Myuu1967/TB-04/ver2/hardware/基板分割_0824/TB04_1_alu/TB04_1_alu.kicad_sch

## KiCad design ver2/hardware/基板分割_0824/TB04_1_alu/TB04_1_alu.kicad_sch (2026-08-24)

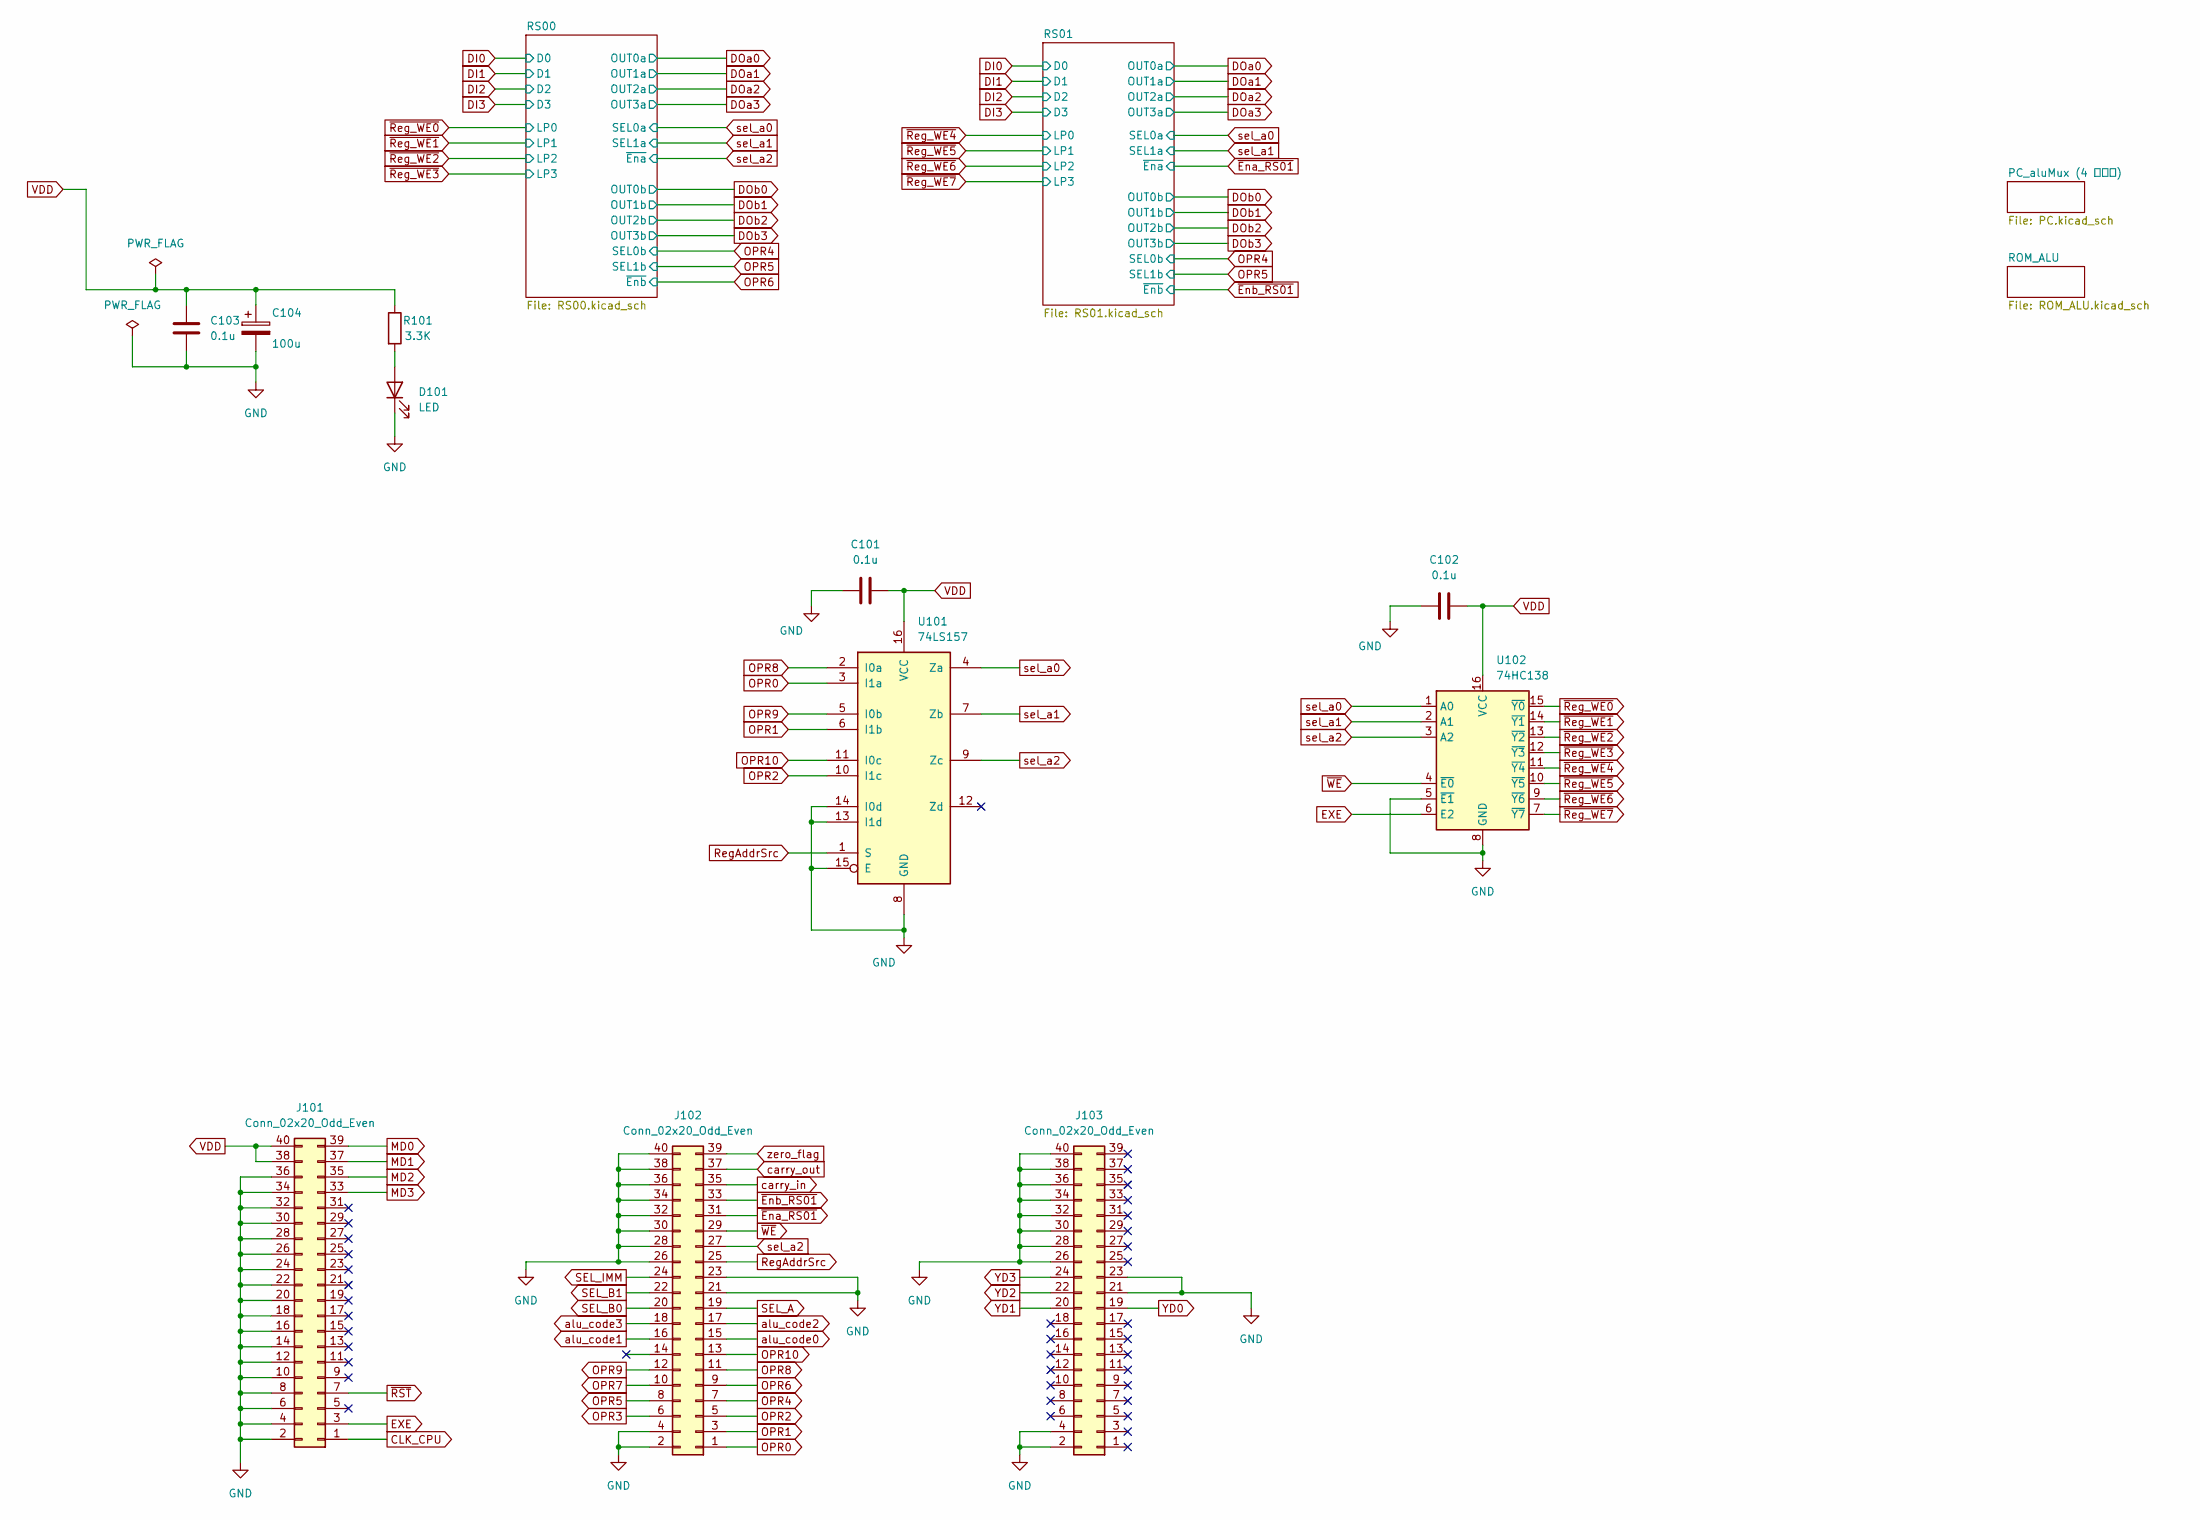
[picture p38: schematic TB04_1_alu.kicad_sch]

Parts:
C101, C102, C103: 0.1u; C_Disc_D4.3mm_W1.9mm_P5.00mm
C104: 100u; CP_Radial_D5.0mm_P2.00mm
D101: LED; LED_D3.0mm_Clear
J101, J102, J103: Conn_02x20_Odd_Even
R101: 3.3K; R_Axial_DIN0207_L6.3mm_D2.5mm_P7.62mm_Horizontal
U101: 74LS157
U102: 74HC138; DIP-16_W7.62mm_Socket

Connections:
CLK_CPU: J101.1
EXE: J101.3, U102.6 (E2)
GND: C101.2, C102.2, C103.2, C104.2, D101.1 (K), J101.2, J101.4, J101.6, J101.8, J101.10, J101.12, J101.14, J101.16, J101.18, J101.20, J101.22, J101.24, J101.26, J101.28, J101.30, J101.32, J101.34, J101.36, J102.2, J102.4, J102.21, J102.23, J102.26, J102.28, J102.30, J102.32, J102.34, J102.36, J102.38, J102.40, J103.2, J103.4, J103.21, J103.23, J103.26, J103.28, J103.30, J103.32, J103.34, J103.36, J103.38, J103.40, U101.8 (GND), U101.13 (I1d), U101.14 (I0d), U101.15 (E), U102.5 (~E1), U102.8 (GND)
MD0: J101.39
MD1: J101.37
MD2: J101.35
MD3: J101.33
unnamed: D101.2 (A), R101.2
OPR0: J102.1, U101.3 (I1a)
OPR1: J102.3, U101.6 (I1b)
OPR2: J102.5, U101.10 (I1c)
OPR3: J102.6
OPR4: J102.7
OPR5: J102.8
OPR6: J102.9
OPR7: J102.10
OPR8: J102.11, U101.2 (I0a)
OPR9: J102.12, U101.5 (I0b)
OPR10: J102.13, U101.11 (I0c)
RegAddrSrc: J102.25, U101.1 (S)
SEL_A: J102.19
SEL_B0: J102.20
SEL_B1: J102.22
SEL_IMM: J102.24
VDD: C101.1, C102.1, C103.1, C104.1, J101.38, J101.40, R101.1, U101.16 (VCC), U102.16 (VCC)
YD0: J103.19
YD1: J103.20
YD2: J103.22
YD3: J103.24
alu_code0: J102.15
alu_code1: J102.16
alu_code2: J102.17
alu_code3: J102.18
carry_in: J102.35
carry_out: J102.37
sel_a0: U101.4 (Za), U102.1 (A0)
sel_a1: U101.7 (Zb), U102.2 (A1)
sel_a2: J102.27, U101.9 (Zc), U102.3 (A2)
zero_flag: J102.39
~Ena_RS01: J102.31
~Enb_RS01: J102.33
~RST: J101.7
~Reg_WE0: U102.15 (~Y0)
~Reg_WE1: U102.14 (~Y1)
~Reg_WE2: U102.13 (~Y2)
~Reg_WE3: U102.12 (~Y3)
~Reg_WE4: U102.11 (~Y4)
~Reg_WE5: U102.10 (~Y5)
~Reg_WE6: U102.9 (~Y6)
~Reg_WE7: U102.7 (~Y7)
~WE: J102.29, U102.4 (~E0)
