Myuu1967/TB-04/ver2/hardware/基板分割_0824/TB04_2_ctrl/ALU.kicad_sch

## KiCad design ver2/hardware/基板分割_0824/TB04_2_ctrl/ALU.kicad_sch (2026-08-24)

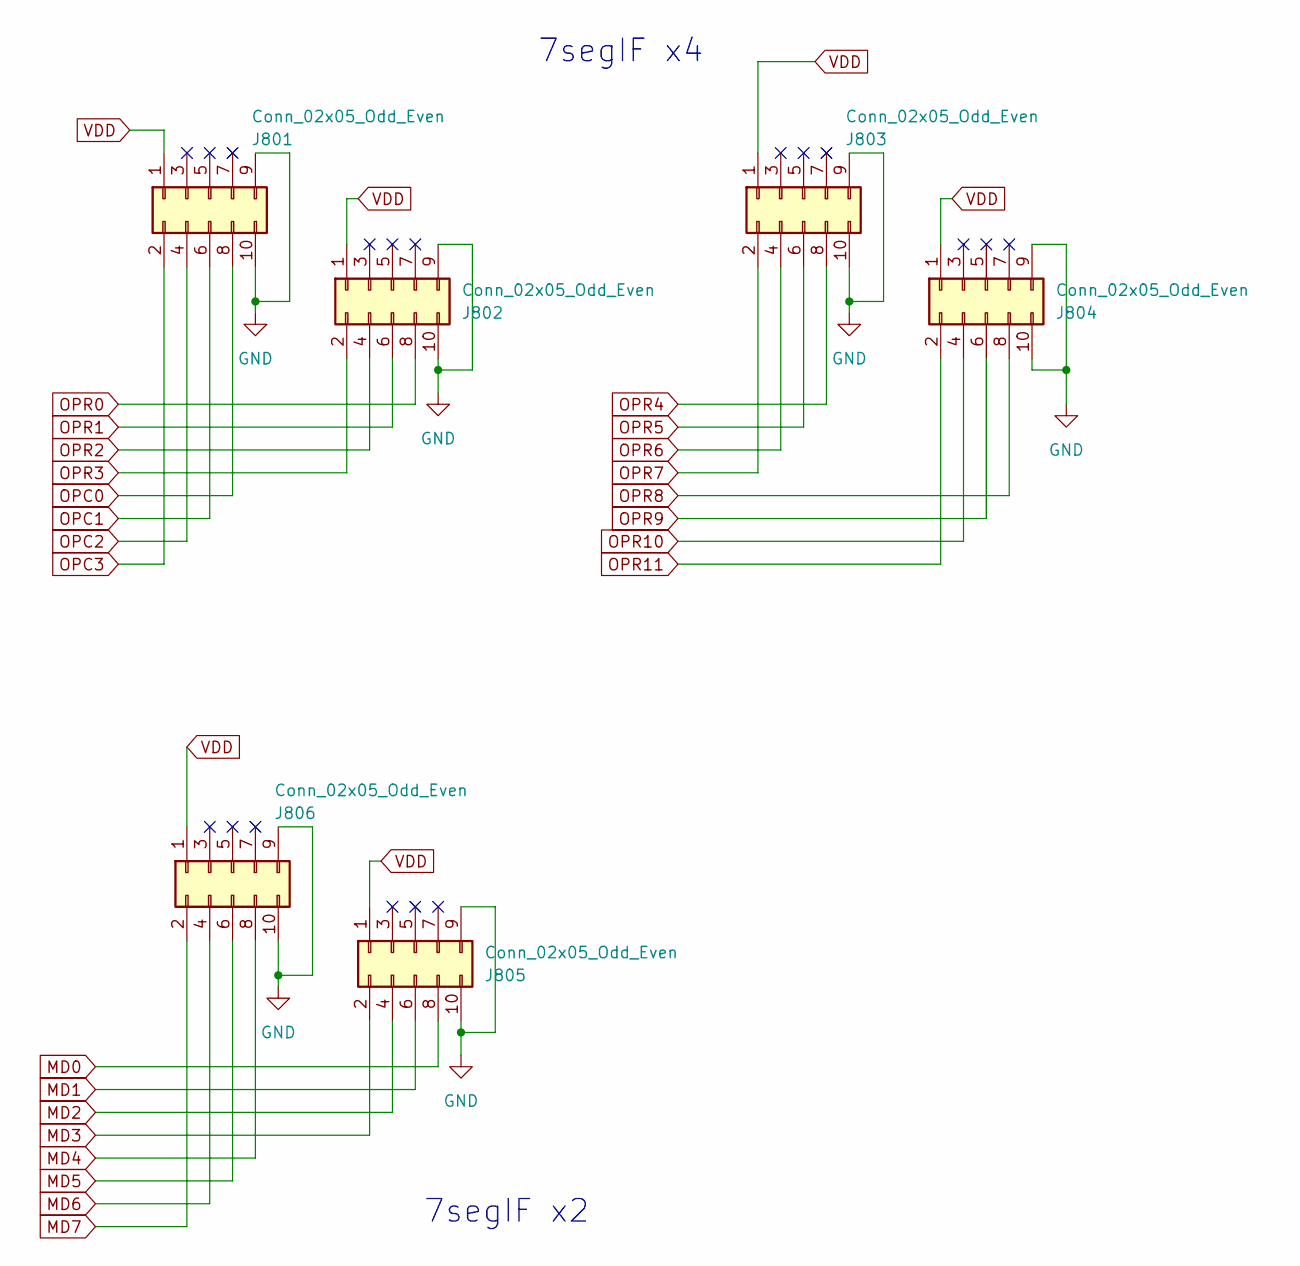
[picture p39: schematic ALU.kicad_sch]

Parts:
J801, J802, J803, J804, J805, J806: Conn_02x05_Odd_Even

Connections:
GND: J801.9, J801.10, J802.9, J802.10, J803.9, J803.10, J804.9, J804.10, J805.9, J805.10, J806.9, J806.10
MD0: J805.8
MD1: J805.6
MD2: J805.4
MD3: J805.2
MD4: J806.8
MD5: J806.6
MD6: J806.4
MD7: J806.2
OPC0: J801.8
OPC1: J801.6
OPC2: J801.4
OPC3: J801.2
OPR0: J802.8
OPR1: J802.6
OPR2: J802.4
OPR3: J802.2
OPR4: J803.8
OPR5: J803.6
OPR6: J803.4
OPR7: J803.2
OPR8: J804.8
OPR9: J804.6
OPR10: J804.4
OPR11: J804.2
VDD: J801.1, J802.1, J803.1, J804.1, J805.1, J806.1

Notes on the sheet:
7segIF x4
7segIF x2
