Myuu1967/TB-04/ver2/hardware/基板分割_0824/TB04_2_ctrl/AddrDecord.kicad_sch

## KiCad design ver2/hardware/基板分割_0824/TB04_2_ctrl/AddrDecord.kicad_sch (2026-08-24)

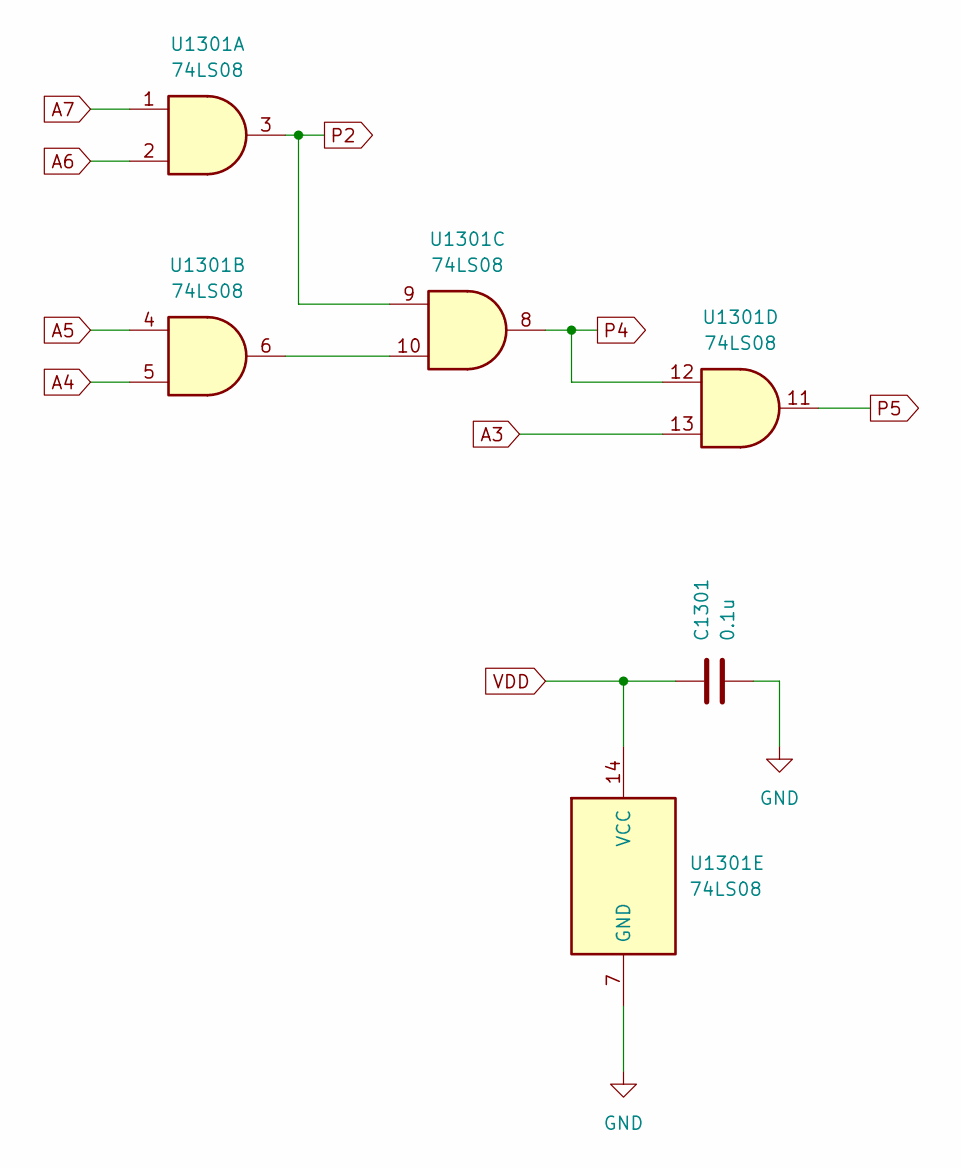
[picture p40: schematic AddrDecord.kicad_sch]

Parts:
C1301: 0.1u
U1301: 74LS08

Connections:
A3: U1301.13
A4: U1301.5
A5: U1301.4
A6: U1301.2
A7: U1301.1
GND: C1301.2, U1301.7 (GND)
unnamed: U1301.6, U1301.10
P2: U1301.3, U1301.9
P4: U1301.8, U1301.12
P5: U1301.11
VDD: C1301.1, U1301.14 (VCC)
