Myuu1967/TB-04/ver2/hardware/基板分割_0824/TB04_2_ctrl/Decoder.kicad_sch

## KiCad design ver2/hardware/基板分割_0824/TB04_2_ctrl/Decoder.kicad_sch (2026-08-24)

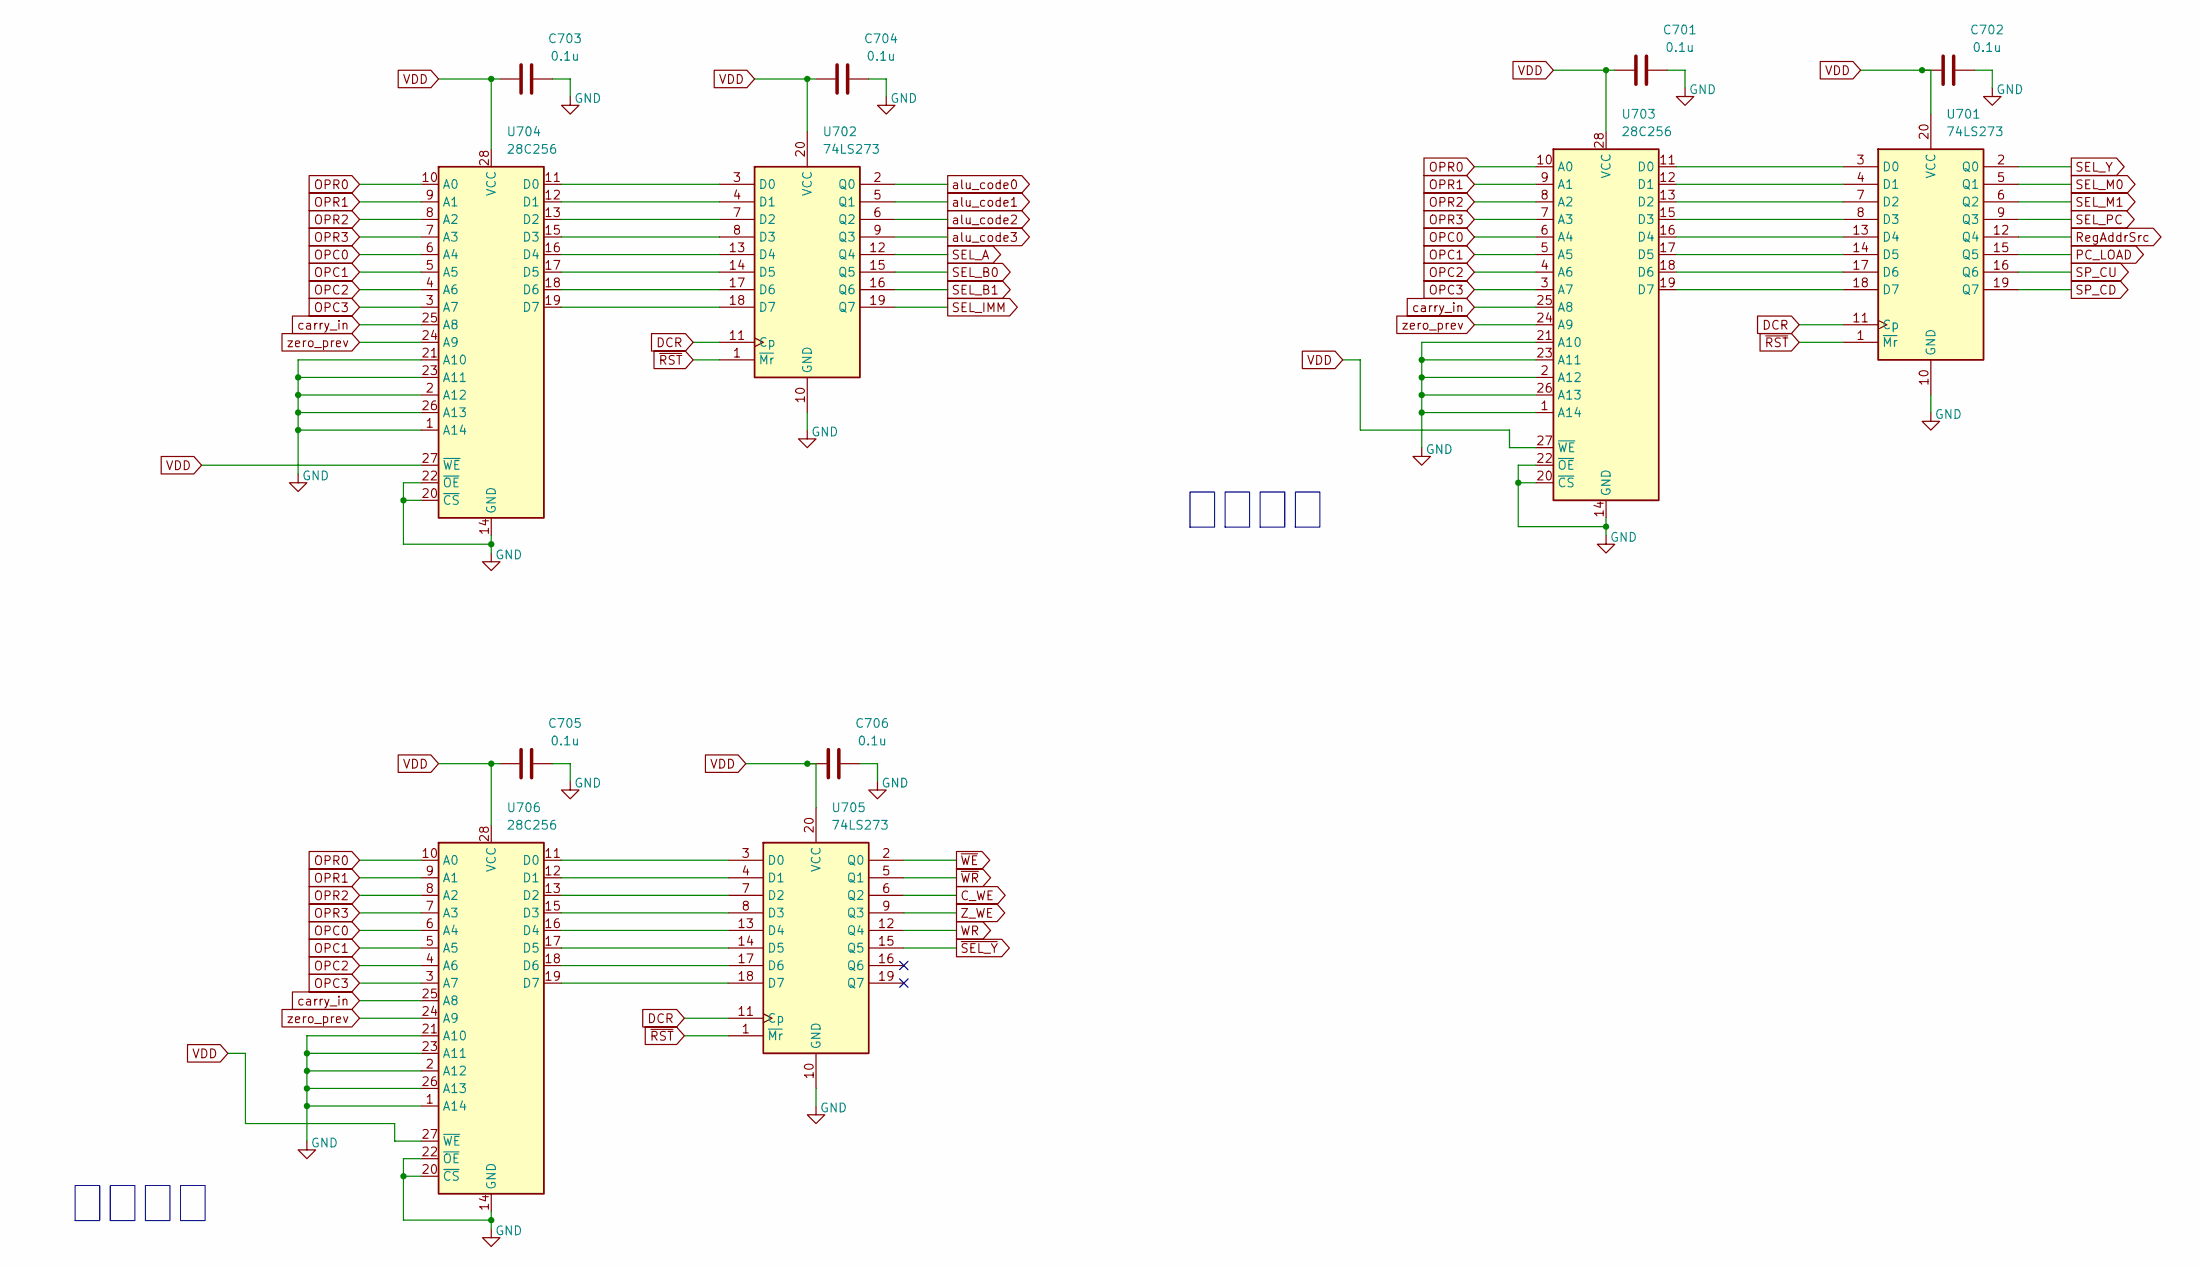
[picture p41: schematic Decoder.kicad_sch]

Parts:
C701, C702, C703, C704, C705, C706: 0.1u; C_Disc_D4.3mm_W1.9mm_P5.00mm
U701, U702, U705: 74LS273; DIP-20_W7.62mm_Socket
U703, U704, U706: 28C256; DIP-28_W15.24mm_Socket

Connections:
C_WE: U705.6 (Q2)
DCR: U701.11 (Cp), U702.11 (Cp), U705.11 (Cp)
GND: C701.1, C702.1, C703.1, C704.1, C705.1, C706.1, U701.10 (GND), U702.10 (GND), U703.1 (A14), U703.2 (A12), U703.14 (GND), U703.20 (~CS), U703.21 (A10), U703.22 (~OE), U703.23 (A11), U703.26 (A13), U704.1 (A14), U704.2 (A12), U704.14 (GND), U704.20 (~CS), U704.21 (A10), U704.22 (~OE), U704.23 (A11), U704.26 (A13), U705.10 (GND), U706.1 (A14), U706.2 (A12), U706.14 (GND), U706.20 (~CS), U706.21 (A10), U706.22 (~OE), U706.23 (A11), U706.26 (A13)
unnamed: U701.3 (D0), U703.11 (D0)
unnamed: U701.4 (D1), U703.12 (D1)
unnamed: U701.7 (D2), U703.13 (D2)
unnamed: U701.8 (D3), U703.15 (D3)
unnamed: U701.13 (D4), U703.16 (D4)
unnamed: U701.14 (D5), U703.17 (D5)
unnamed: U701.17 (D6), U703.18 (D6)
unnamed: U701.18 (D7), U703.19 (D7)
unnamed: U702.3 (D0), U704.11 (D0)
unnamed: U702.4 (D1), U704.12 (D1)
unnamed: U702.7 (D2), U704.13 (D2)
unnamed: U702.8 (D3), U704.15 (D3)
unnamed: U702.13 (D4), U704.16 (D4)
unnamed: U702.14 (D5), U704.17 (D5)
unnamed: U702.17 (D6), U704.18 (D6)
unnamed: U702.18 (D7), U704.19 (D7)
unnamed: U705.3 (D0), U706.11 (D0)
unnamed: U705.4 (D1), U706.12 (D1)
unnamed: U705.7 (D2), U706.13 (D2)
unnamed: U705.8 (D3), U706.15 (D3)
unnamed: U705.13 (D4), U706.16 (D4)
unnamed: U705.14 (D5), U706.17 (D5)
unnamed: U705.17 (D6), U706.18 (D6)
unnamed: U705.18 (D7), U706.19 (D7)
OPC0: U703.6 (A4), U704.6 (A4), U706.6 (A4)
OPC1: U703.5 (A5), U704.5 (A5), U706.5 (A5)
OPC2: U703.4 (A6), U704.4 (A6), U706.4 (A6)
OPC3: U703.3 (A7), U704.3 (A7), U706.3 (A7)
OPR0: U703.10 (A0), U704.10 (A0), U706.10 (A0)
OPR1: U703.9 (A1), U704.9 (A1), U706.9 (A1)
OPR2: U703.8 (A2), U704.8 (A2), U706.8 (A2)
OPR3: U703.7 (A3), U704.7 (A3), U706.7 (A3)
PC_LOAD: U701.15 (Q5)
RegAddrSrc: U701.12 (Q4)
SEL_A: U702.12 (Q4)
SEL_B0: U702.15 (Q5)
SEL_B1: U702.16 (Q6)
SEL_IMM: U702.19 (Q7)
SEL_M0: U701.5 (Q1)
SEL_M1: U701.6 (Q2)
SEL_PC: U701.9 (Q3)
SEL_Y: U701.2 (Q0)
SP_CD: U701.19 (Q7)
SP_CU: U701.16 (Q6)
VDD: C701.2, C702.2, C703.2, C704.2, C705.2, C706.2, U701.20 (VCC), U702.20 (VCC), U703.27 (~WE), U703.28 (VCC), U704.27 (~WE), U704.28 (VCC), U705.20 (VCC), U706.27 (~WE), U706.28 (VCC)
WR: U705.12 (Q4)
Z_WE: U705.9 (Q3)
alu_code0: U702.2 (Q0)
alu_code1: U702.5 (Q1)
alu_code2: U702.6 (Q2)
alu_code3: U702.9 (Q3)
carry_in: U703.25 (A8), U704.25 (A8), U706.25 (A8)
zero_prev: U703.24 (A9), U704.24 (A9), U706.24 (A9)
~RST: U701.1 (~Mr), U702.1 (~Mr), U705.1 (~Mr)
~SEL_Y: U705.15 (Q5)
~WE: U705.2 (Q0)
~WR: U705.5 (Q1)

Notes on the sheet:
デコーダ
