Myuu1967/TB-04/ver2/hardware/基板分割_0824/TB04_2_ctrl/TB04_2_ctrl.kicad_sch

## KiCad design ver2/hardware/基板分割_0824/TB04_2_ctrl/TB04_2_ctrl.kicad_sch (2026-08-24)

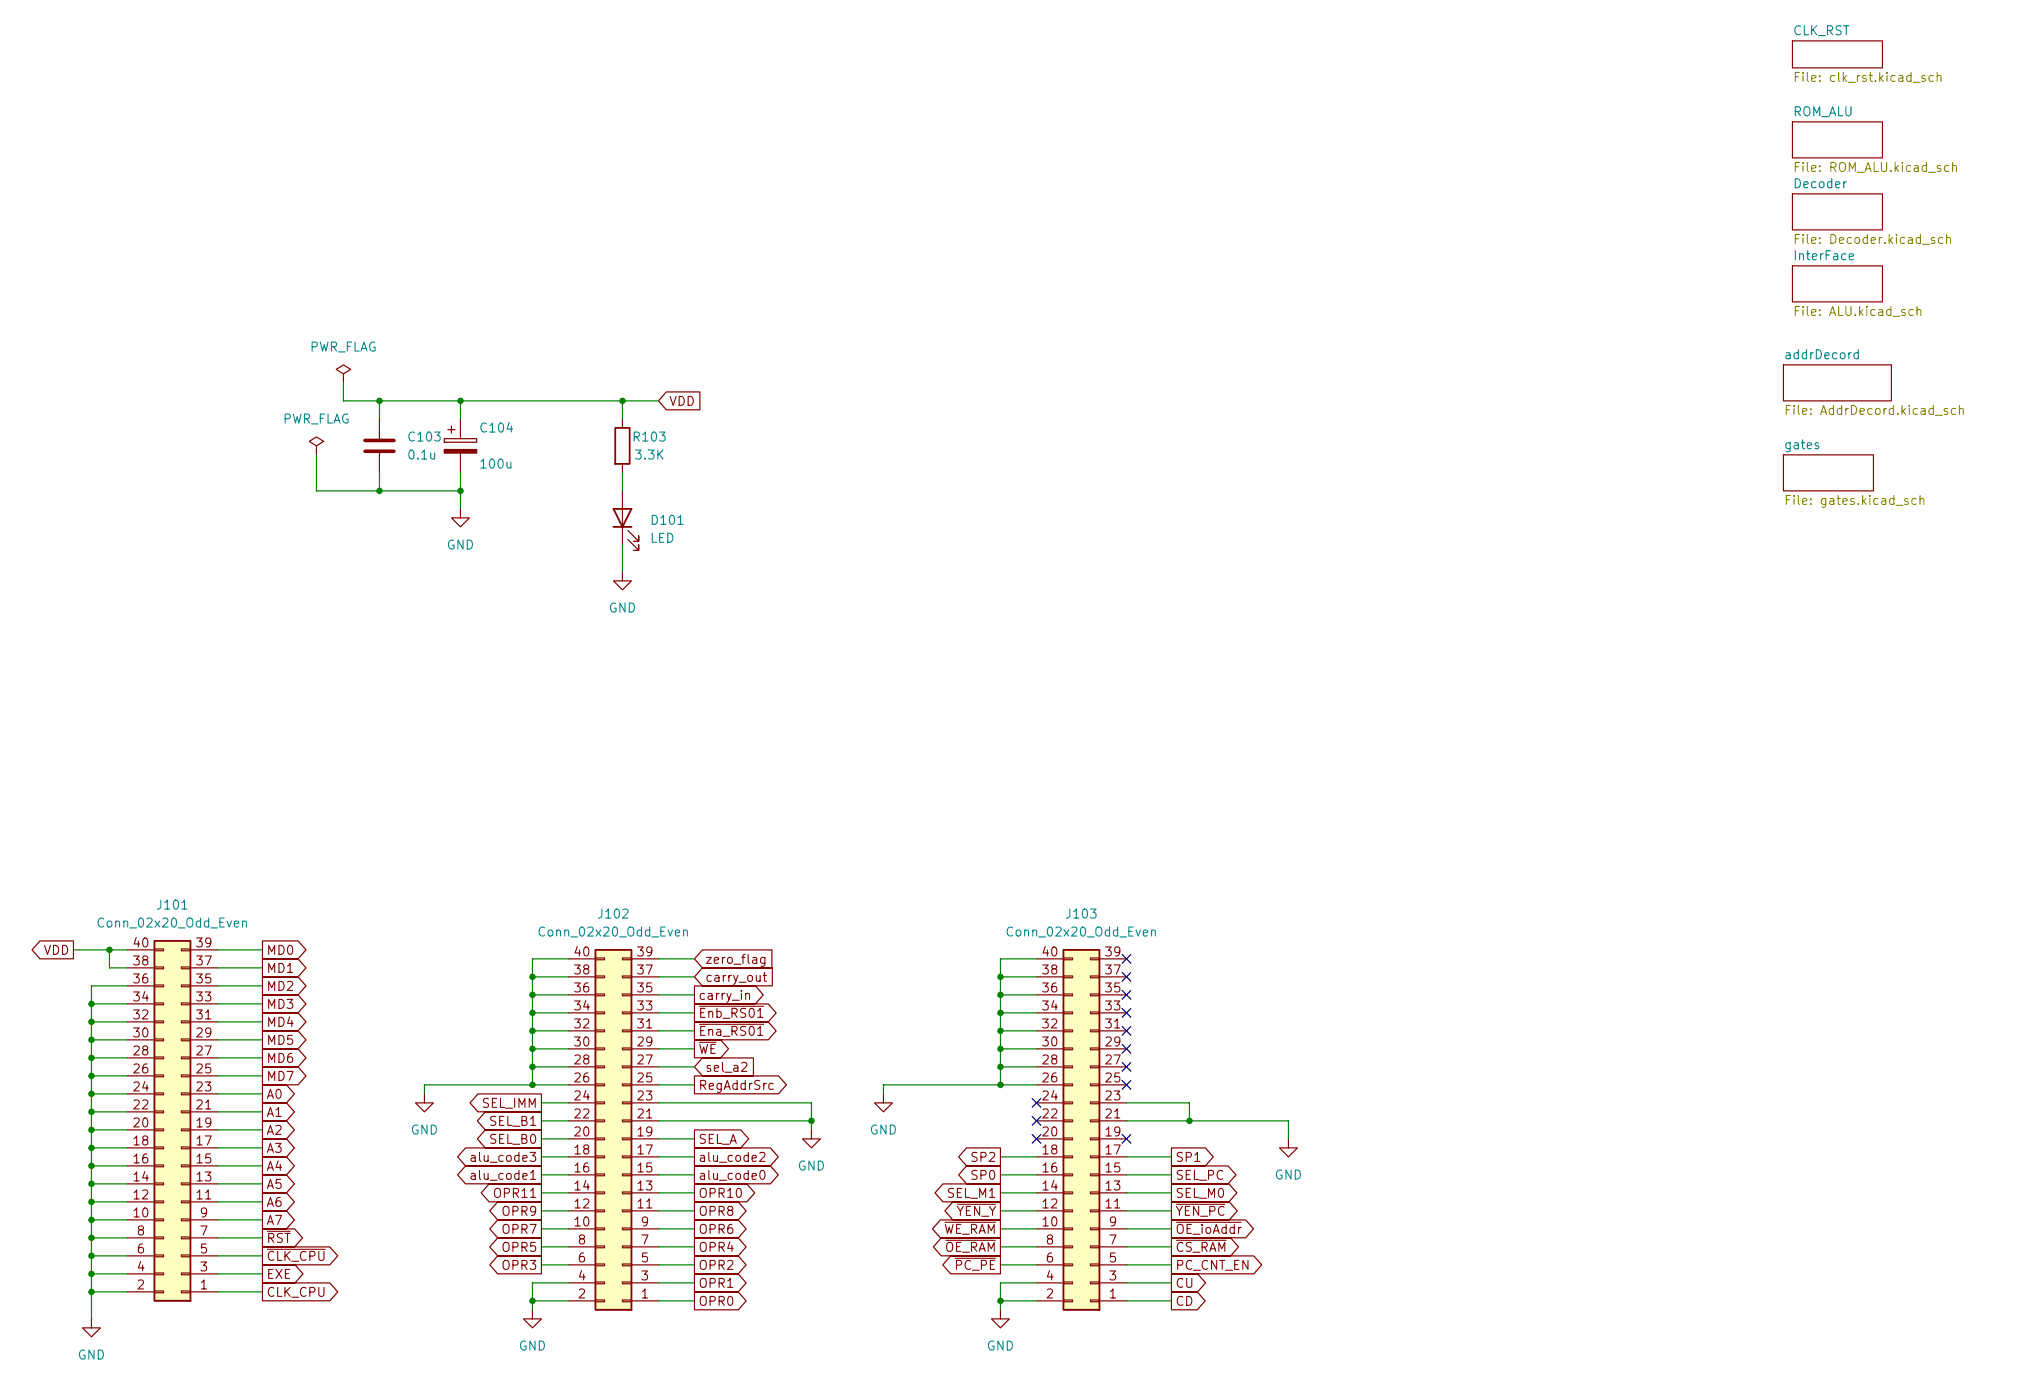
[picture p43: schematic TB04_2_ctrl.kicad_sch]

Parts:
C103: 0.1u; C_Disc_D4.3mm_W1.9mm_P5.00mm
C104: 100u; CP_Radial_D5.0mm_P2.00mm
D101: LED; LED_D3.0mm_Clear
J101, J102, J103: Conn_02x20_Odd_Even
R103: 3.3K; R_Axial_DIN0207_L6.3mm_D2.5mm_P7.62mm_Horizontal

Connections:
A0: J101.23
A1: J101.21
A2: J101.19
A3: J101.17
A4: J101.15
A5: J101.13
A6: J101.11
A7: J101.9
CD: J103.1
CLK_CPU: J101.1
CU: J103.3
EXE: J101.3
GND: C103.2, C104.2, D101.1 (K), J101.2, J101.4, J101.6, J101.8, J101.10, J101.12, J101.14, J101.16, J101.18, J101.20, J101.22, J101.24, J101.26, J101.28, J101.30, J101.32, J101.34, J101.36, J102.2, J102.4, J102.21, J102.23, J102.26, J102.28, J102.30, J102.32, J102.34, J102.36, J102.38, J102.40, J103.2, J103.4, J103.21, J103.23, J103.26, J103.28, J103.30, J103.32, J103.34, J103.36, J103.38, J103.40
MD0: J101.39
MD1: J101.37
MD2: J101.35
MD3: J101.33
MD4: J101.31
MD5: J101.29
MD6: J101.27
MD7: J101.25
unnamed: D101.2 (A), R103.2
OPR0: J102.1
OPR1: J102.3
OPR2: J102.5
OPR3: J102.6
OPR4: J102.7
OPR5: J102.8
OPR6: J102.9
OPR7: J102.10
OPR8: J102.11
OPR9: J102.12
OPR10: J102.13
OPR11: J102.14
PC_CNT_EN: J103.5
RegAddrSrc: J102.25
SEL_A: J102.19
SEL_B0: J102.20
SEL_B1: J102.22
SEL_IMM: J102.24
SEL_M0: J103.13
SEL_M1: J103.14
SEL_PC: J103.15
SP0: J103.16
SP1: J103.17
SP2: J103.18
VDD: C103.1, C104.1, J101.38, J101.40, R103.1
alu_code0: J102.15
alu_code1: J102.16
alu_code2: J102.17
alu_code3: J102.18
carry_in: J102.35
carry_out: J102.37
sel_a2: J102.27
zero_flag: J102.39
~CLK_CPU: J101.5
~CS_RAM: J103.7
~Ena_RS01: J102.31
~Enb_RS01: J102.33
~OE_RAM: J103.8
~OE_ioAddr: J103.9
~PC_PE: J103.6
~RST: J101.7
~WE_RAM: J103.10
~WE: J102.29
~YEN_PC: J103.11
~YEN_Y: J103.12
