Myuu1967/TB-04/ver2/hardware/基板分割_0824/TB04_2_ctrl/clk_rst.kicad_sch

## KiCad design ver2/hardware/基板分割_0824/TB04_2_ctrl/clk_rst.kicad_sch (2026-08-24)

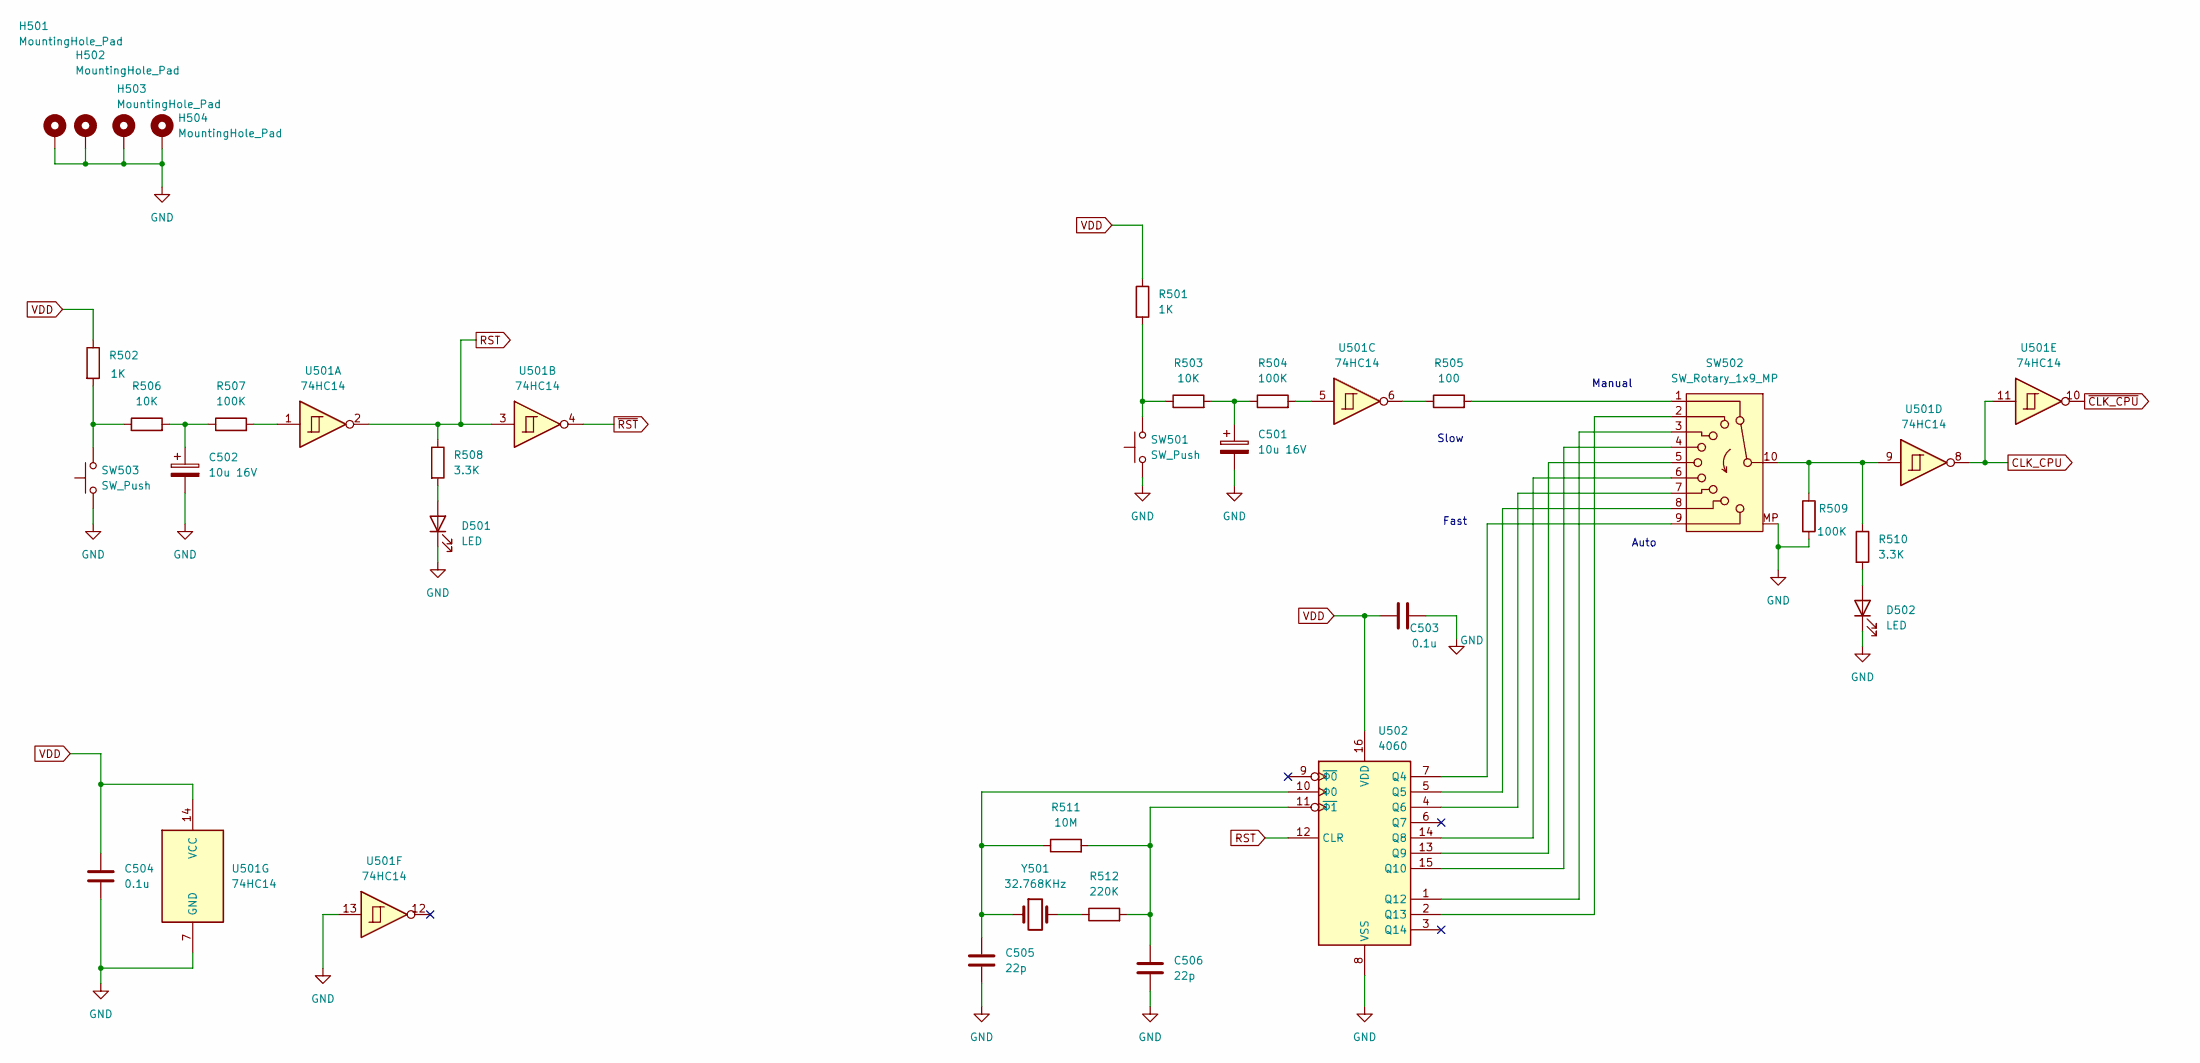
[picture p44: schematic clk_rst.kicad_sch]

Parts:
C501, C502: 10u 16V; CP_Radial_D5.0mm_P2.00mm
C503, C504: 0.1u; C_Disc_D4.3mm_W1.9mm_P5.00mm
C505, C506: 22p
D501, D502: LED; LED_D3.0mm_Clear
H501, H502, H503, H504: MountingHole_Pad; MountingHole_3.2mm_M3_Pad_Via
R501, R502: 1K; R_Axial_DIN0207_L6.3mm_D2.5mm_P10.16mm_Horizontal
R503, R506: 10K; R_Axial_DIN0207_L6.3mm_D2.5mm_P10.16mm_Horizontal
R504, R507: 100K; R_Axial_DIN0207_L6.3mm_D2.5mm_P7.62mm_Horizontal
R505: 100; R_Axial_DIN0207_L6.3mm_D2.5mm_P10.16mm_Horizontal
R508, R510: 3.3K; R_Axial_DIN0207_L6.3mm_D2.5mm_P7.62mm_Horizontal
R509: 100K
R511: 10M
R512: 220K
SW501, SW503: SW_Push; SW_Tactile_Straight_KSL0Axx1LFTR
SW502: SW_Rotary_1x9_MP
U501: 74HC14; DIP-14_W7.62mm_Socket
U502: 4060
Y501: 32.768KHz

Connections:
CLK_CPU: U501.8, U501.11
GND: C501.2, C502.2, C503.1, C504.2, C505.2, C506.2, D501.1 (K), D502.1 (K), H501.1, H502.1, H503.1, H504.1, R509.2, SW501.1, SW502.MP, SW503.1, U501.7 (GND), U501.13, U502.8 (VSS)
unnamed: C501.1, R503.2, R504.1
unnamed: C502.1, R506.2, R507.1
unnamed: C505.1, R511.1, U502.10 (Φ0), Y501.1
unnamed: C506.1, R511.2, R512.2, U502.11 (~Φ1)
unnamed: D501.2 (A), R508.2
unnamed: D502.2 (A), R510.2
unnamed: R501.2, R503.1, SW501.2
unnamed: R502.2, R506.1, SW503.2
unnamed: R504.2, U501.5
unnamed: R505.1, U501.6
unnamed: R505.2, SW502.1
unnamed: R507.2, U501.1
unnamed: R509.1, R510.1, SW502.10, U501.9
unnamed: R512.1, Y501.2
unnamed: SW502.2, U502.2 (Q13)
unnamed: SW502.3, U502.1 (Q12)
unnamed: SW502.4, U502.15 (Q10)
unnamed: SW502.5, U502.13 (Q9)
unnamed: SW502.6, U502.14 (Q8)
unnamed: SW502.7, U502.4 (Q6)
unnamed: SW502.8, U502.5 (Q5)
unnamed: SW502.9, U502.7 (Q4)
RST: R508.1, U501.2, U501.3, U502.12 (CLR)
VDD: C503.2, C504.1, R501.1, R502.1, U501.14 (VCC), U502.16 (VDD)
~CLK_CPU: U501.10
~RST: U501.4

Notes on the sheet:
Auto
Manual
Slow
Fast
