Myuu1967/TB-04/ver2/hardware/基板分割_0824/TB04_2_ctrl/gates.kicad_sch

## KiCad design ver2/hardware/基板分割_0824/TB04_2_ctrl/gates.kicad_sch (2026-08-24)

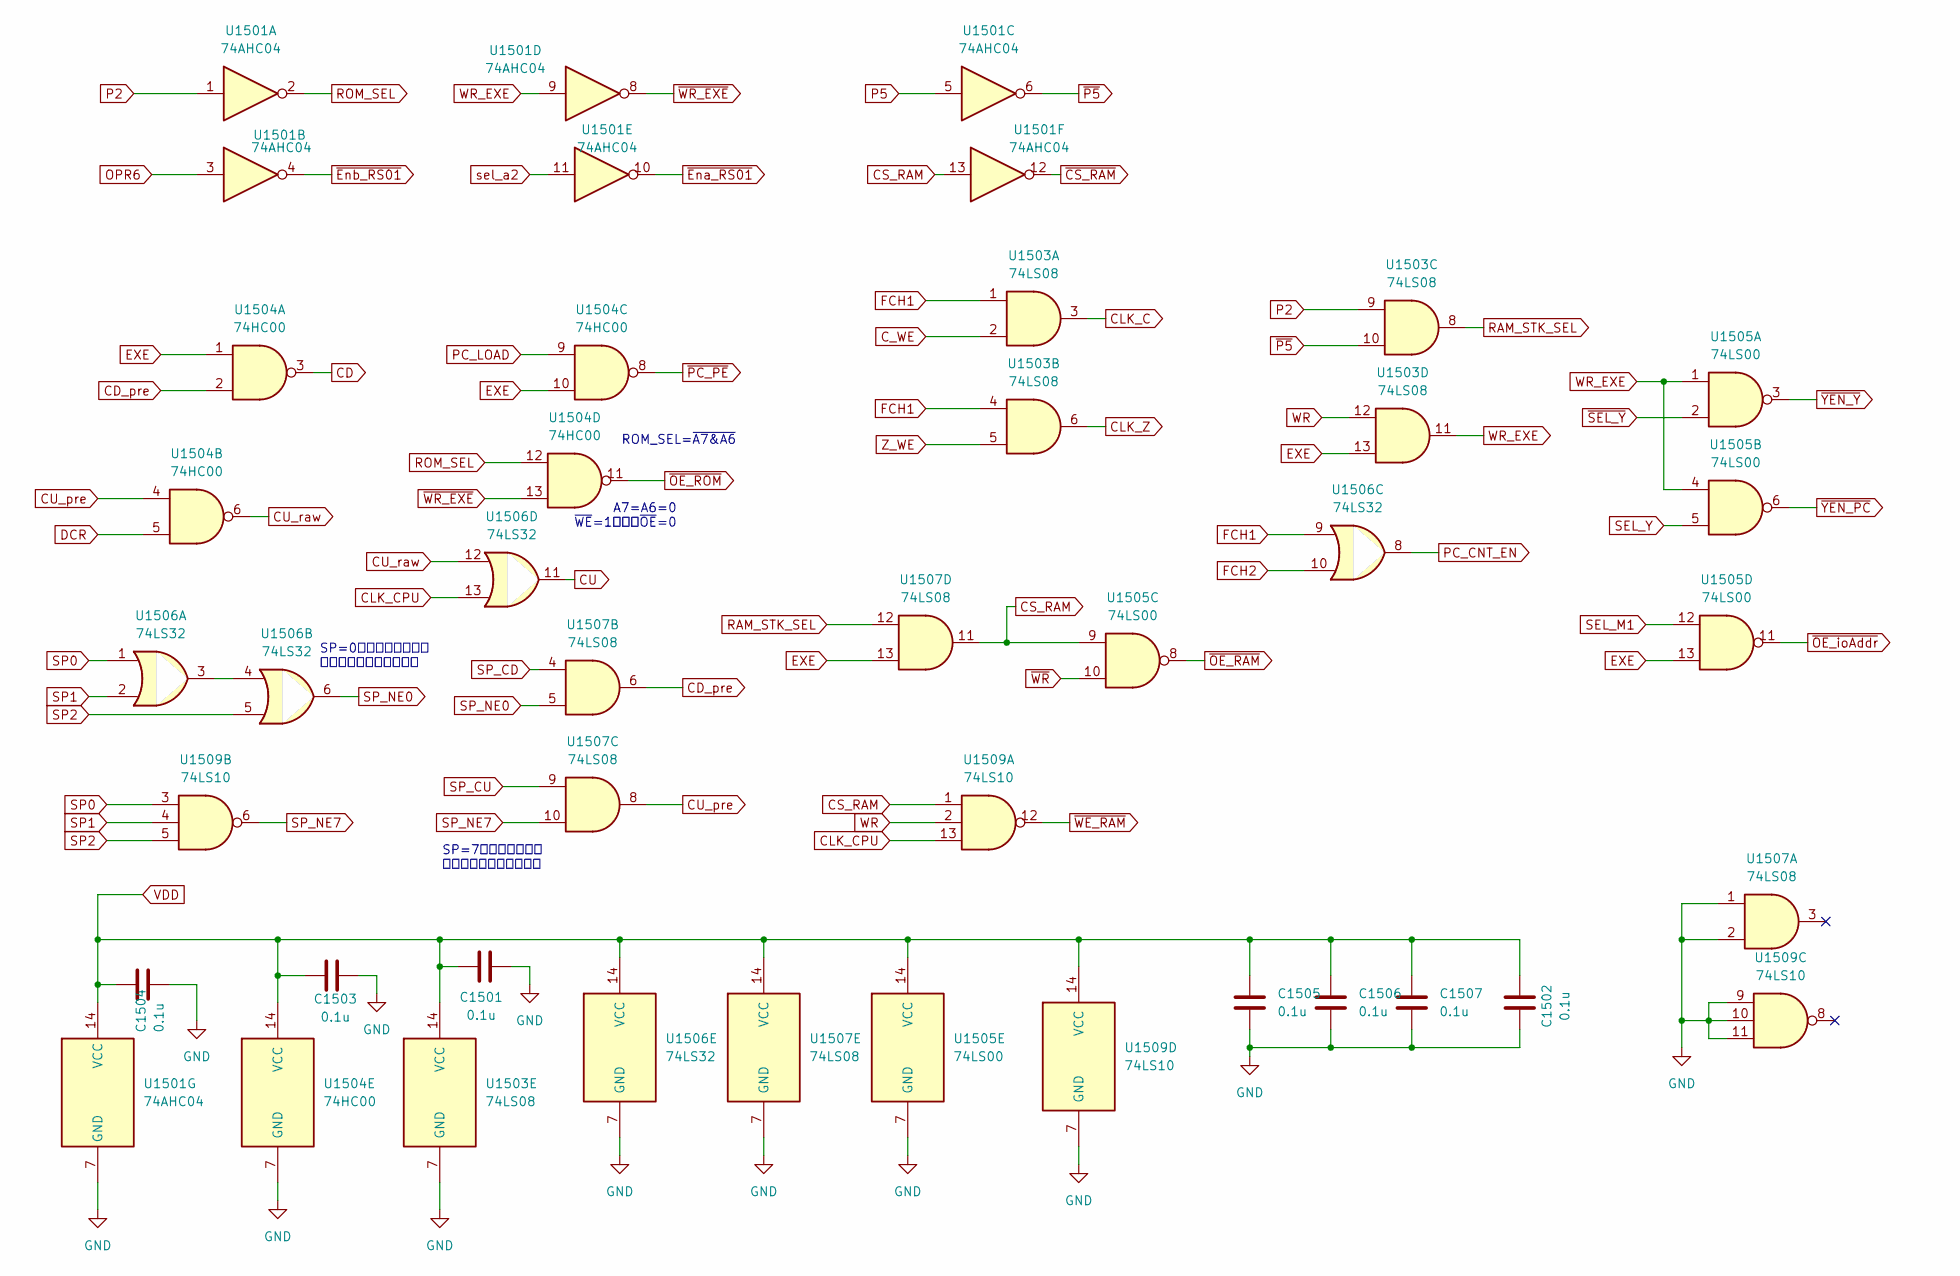
[picture p45: schematic gates.kicad_sch]

Parts:
C1501, C1502, C1503: 0.1u; C_Disc_D4.3mm_W1.9mm_P5.00mm
C1504, C1505, C1506, C1507: 0.1u
U1501: 74AHC04
U1503, U1507: 74LS08
U1504: 74HC00
U1505: 74LS00
U1506: 74LS32
U1509: 74LS10

Connections:
CD: U1504.3
CD_pre: U1504.2, U1507.6
CLK_C: U1503.3
CLK_CPU: U1506.13, U1509.13
CLK_Z: U1503.6
CS_RAM: U1501.13, U1505.9, U1507.11, U1509.1
CU: U1506.11
CU_pre: U1504.4, U1507.8
CU_raw: U1504.6, U1506.12
C_WE: U1503.2
DCR: U1504.5
EXE: U1503.13, U1504.1, U1504.10, U1505.13, U1507.13
FCH1: U1503.1, U1503.4, U1506.9
FCH2: U1506.10
GND: C1501.2, C1502.1, C1503.2, C1504.2, C1505.1, C1506.1, C1507.1, U1501.7 (GND), U1503.7 (GND), U1504.7 (GND), U1505.7 (GND), U1506.7 (GND), U1507.1, U1507.2, U1507.7 (GND), U1509.7 (GND), U1509.9, U1509.10, U1509.11
unnamed: U1506.3, U1506.4
OPR6: U1501.3
P2: U1501.1, U1503.9
P5: U1501.5
PC_CNT_EN: U1506.8
PC_LOAD: U1504.9
RAM_STK_SEL: U1503.8, U1507.12
ROM_SEL: U1501.2, U1504.12
SEL_M1: U1505.12
SEL_Y: U1505.5
SP0: U1506.1, U1509.3
SP1: U1506.2, U1509.4
SP2: U1506.5, U1509.5
SP_CD: U1507.4
SP_CU: U1507.9
SP_NE0: U1506.6, U1507.5
SP_NE7: U1507.10, U1509.6
VDD: C1501.1, C1502.2, C1503.1, C1504.1, C1505.2, C1506.2, C1507.2, U1501.14 (VCC), U1503.14 (VCC), U1504.14 (VCC), U1505.14 (VCC), U1506.14 (VCC), U1507.14 (VCC), U1509.14 (VCC)
WR: U1503.12, U1509.2
WR_EXE: U1501.9, U1503.11, U1505.1, U1505.4
Z_WE: U1503.5
sel_a2: U1501.11
~CS_RAM: U1501.12
~Ena_RS01: U1501.10
~Enb_RS01: U1501.4
~OE_RAM: U1505.8
~OE_ROM: U1504.11
~OE_ioAddr: U1505.11
~P5: U1501.6, U1503.10
~PC_PE: U1504.8
~SEL_Y: U1505.2
~WE_RAM: U1509.12
~WR_EXE: U1501.8, U1504.13
~WR: U1505.10
~YEN_PC: U1505.6
~YEN_Y: U1505.3

Notes on the sheet:
ROM_SEL=~{A7&A6}
A7=A6=0 ~{WE}=1のとき~{OE}=0
SP=7のときそれ以上 カウントアップさせない
SP=0のときそれ以下に カウントダウンさせない
