Myuu1967/TB-04/ver2/hardware/基板分割_0824/TB04_4_io/TB04_4_io.kicad_sch

## KiCad design ver2/hardware/基板分割_0824/TB04_4_io/TB04_4_io.kicad_sch (2026-08-24)

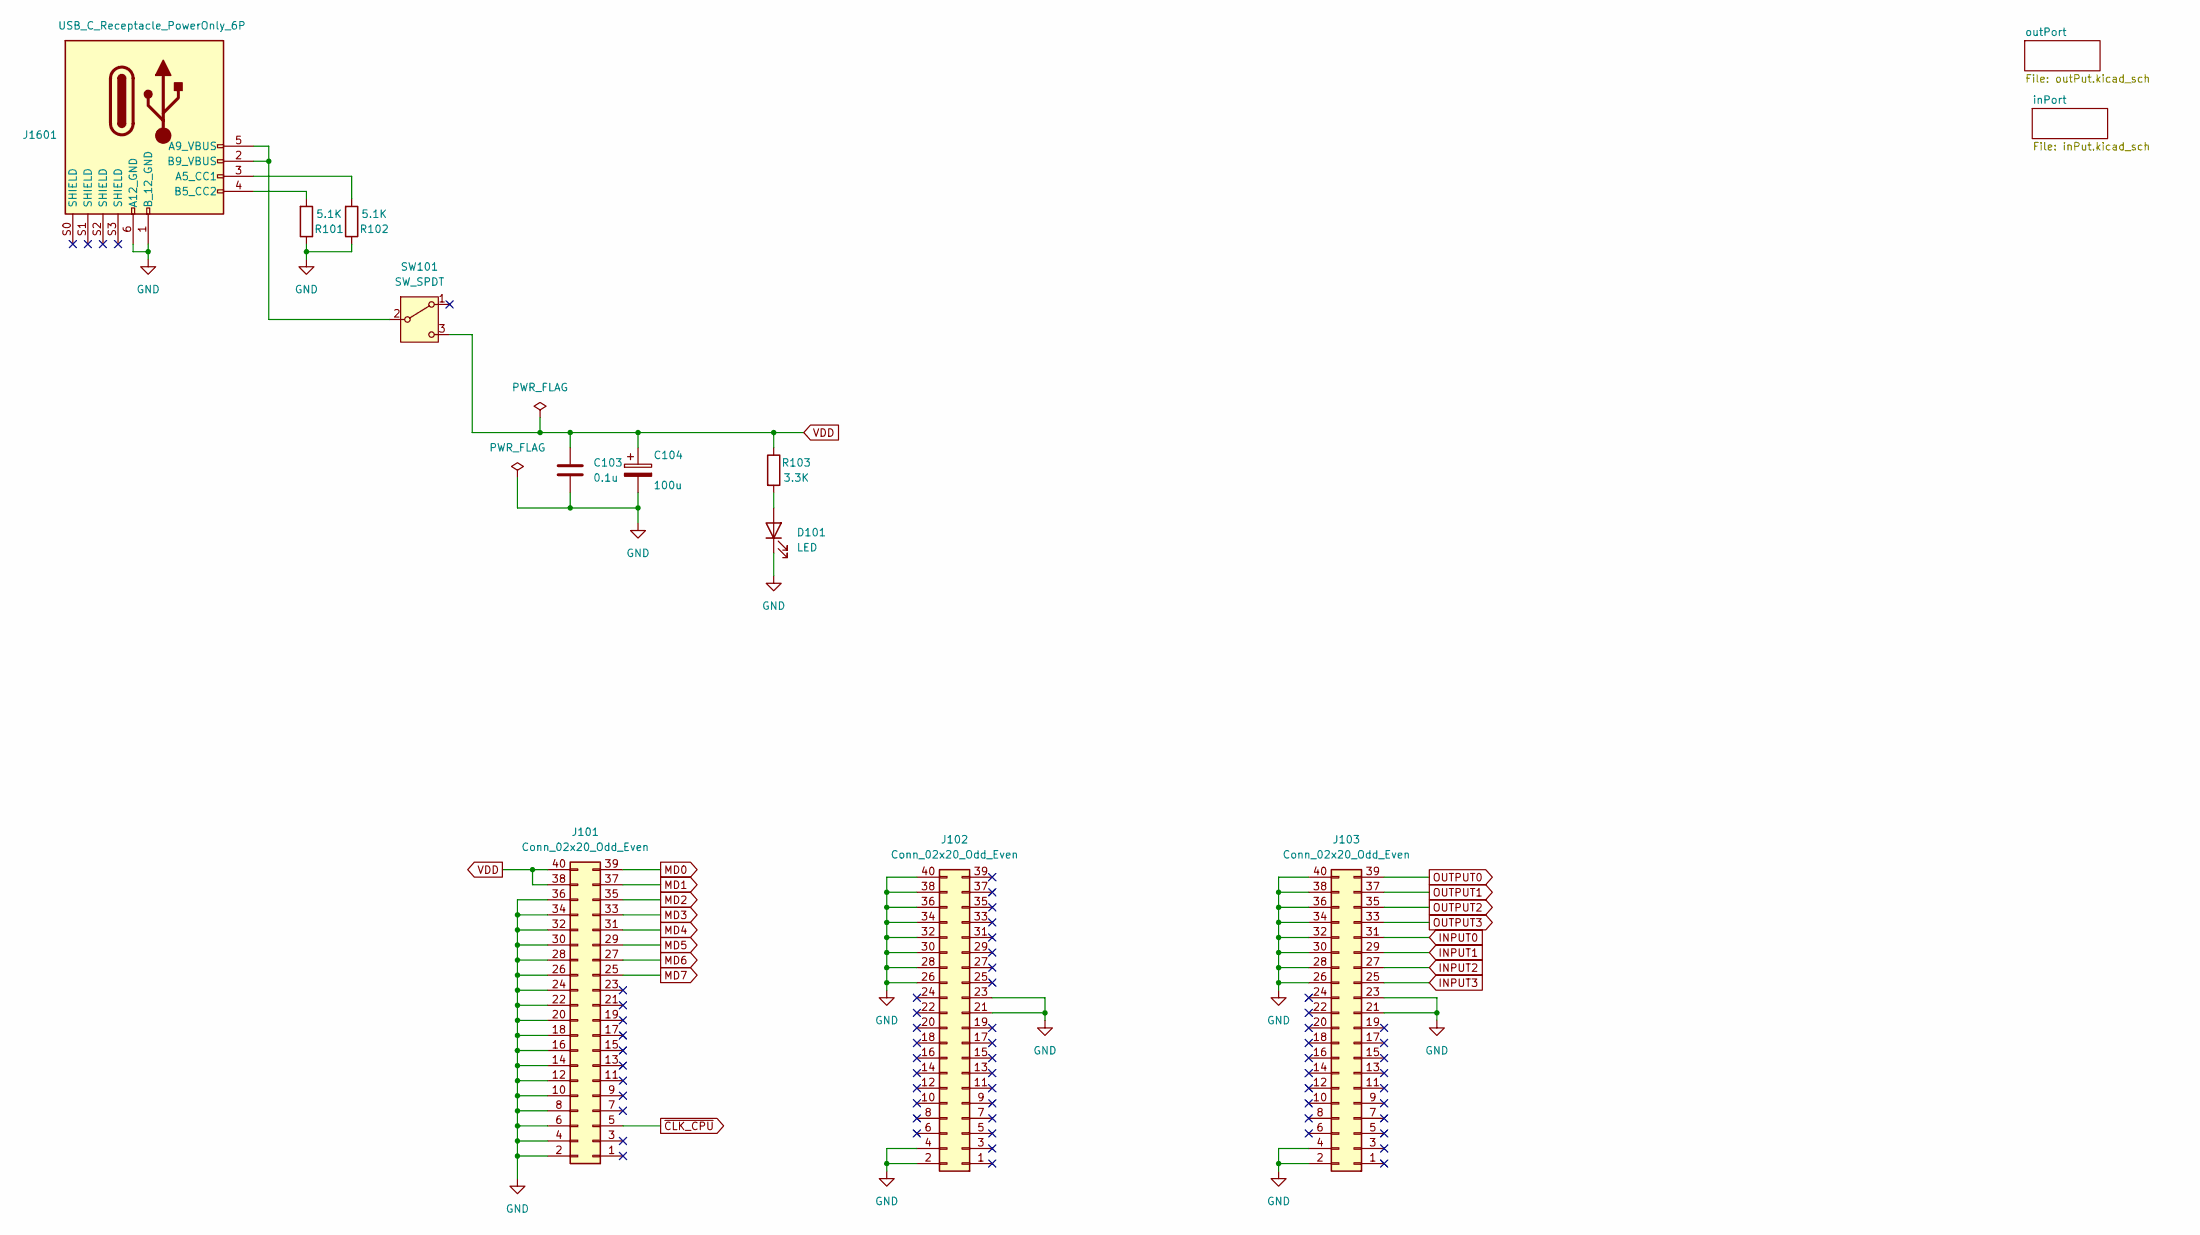
[picture p46: schematic TB04_4_io.kicad_sch]

Parts:
C103: 0.1u; C_Disc_D4.3mm_W1.9mm_P5.00mm
C104: 100u; CP_Radial_D5.0mm_P2.00mm
D101: LED; LED_D3.0mm_Clear
J101, J102, J103: Conn_02x20_Odd_Even
J1601: USB_C_Receptacle_PowerOnly_6P; USB_C_receptacle_onlypower_tanuki
R101, R102: 5.1K; R_Axial_DIN0207_L6.3mm_D2.5mm_P10.16mm_Horizontal
R103: 3.3K; R_Axial_DIN0207_L6.3mm_D2.5mm_P7.62mm_Horizontal
SW101: SW_SPDT; sw_slide

Connections:
GND: C103.2, C104.2, D101.1 (K), J101.2, J101.4, J101.6, J101.8, J101.10, J101.12, J101.14, J101.16, J101.18, J101.20, J101.22, J101.24, J101.26, J101.28, J101.30, J101.32, J101.34, J101.36, J102.2, J102.4, J102.21, J102.23, J102.26, J102.28, J102.30, J102.32, J102.34, J102.36, J102.38, J102.40, J103.2, J103.4, J103.21, J103.23, J103.26, J103.28, J103.30, J103.32, J103.34, J103.36, J103.38, J103.40, J1601.1 (B_12_GND), J1601.6 (A12_GND), R101.1, R102.1
INPUT0: J103.31
INPUT1: J103.29
INPUT2: J103.27
INPUT3: J103.25
MD0: J101.39
MD1: J101.37
MD2: J101.35
MD3: J101.33
MD4: J101.31
MD5: J101.29
MD6: J101.27
MD7: J101.25
unnamed: D101.2 (A), R103.2
unnamed: J1601.2 (B9_VBUS), J1601.5 (A9_VBUS), SW101.2 (B)
unnamed: J1601.3 (A5_CC1), R102.2
unnamed: J1601.4 (B5_CC2), R101.2
OUTPUT0: J103.39
OUTPUT1: J103.37
OUTPUT2: J103.35
OUTPUT3: J103.33
VDD: C103.1, C104.1, J101.38, J101.40, R103.1, SW101.3 (C)
~CLK_CPU: J101.5
