Myuu1967/TB-04/ver2/hardware/基板分割_0824/TB04_4_io/inPut.kicad_sch

## KiCad design ver2/hardware/基板分割_0824/TB04_4_io/inPut.kicad_sch (2026-08-24)

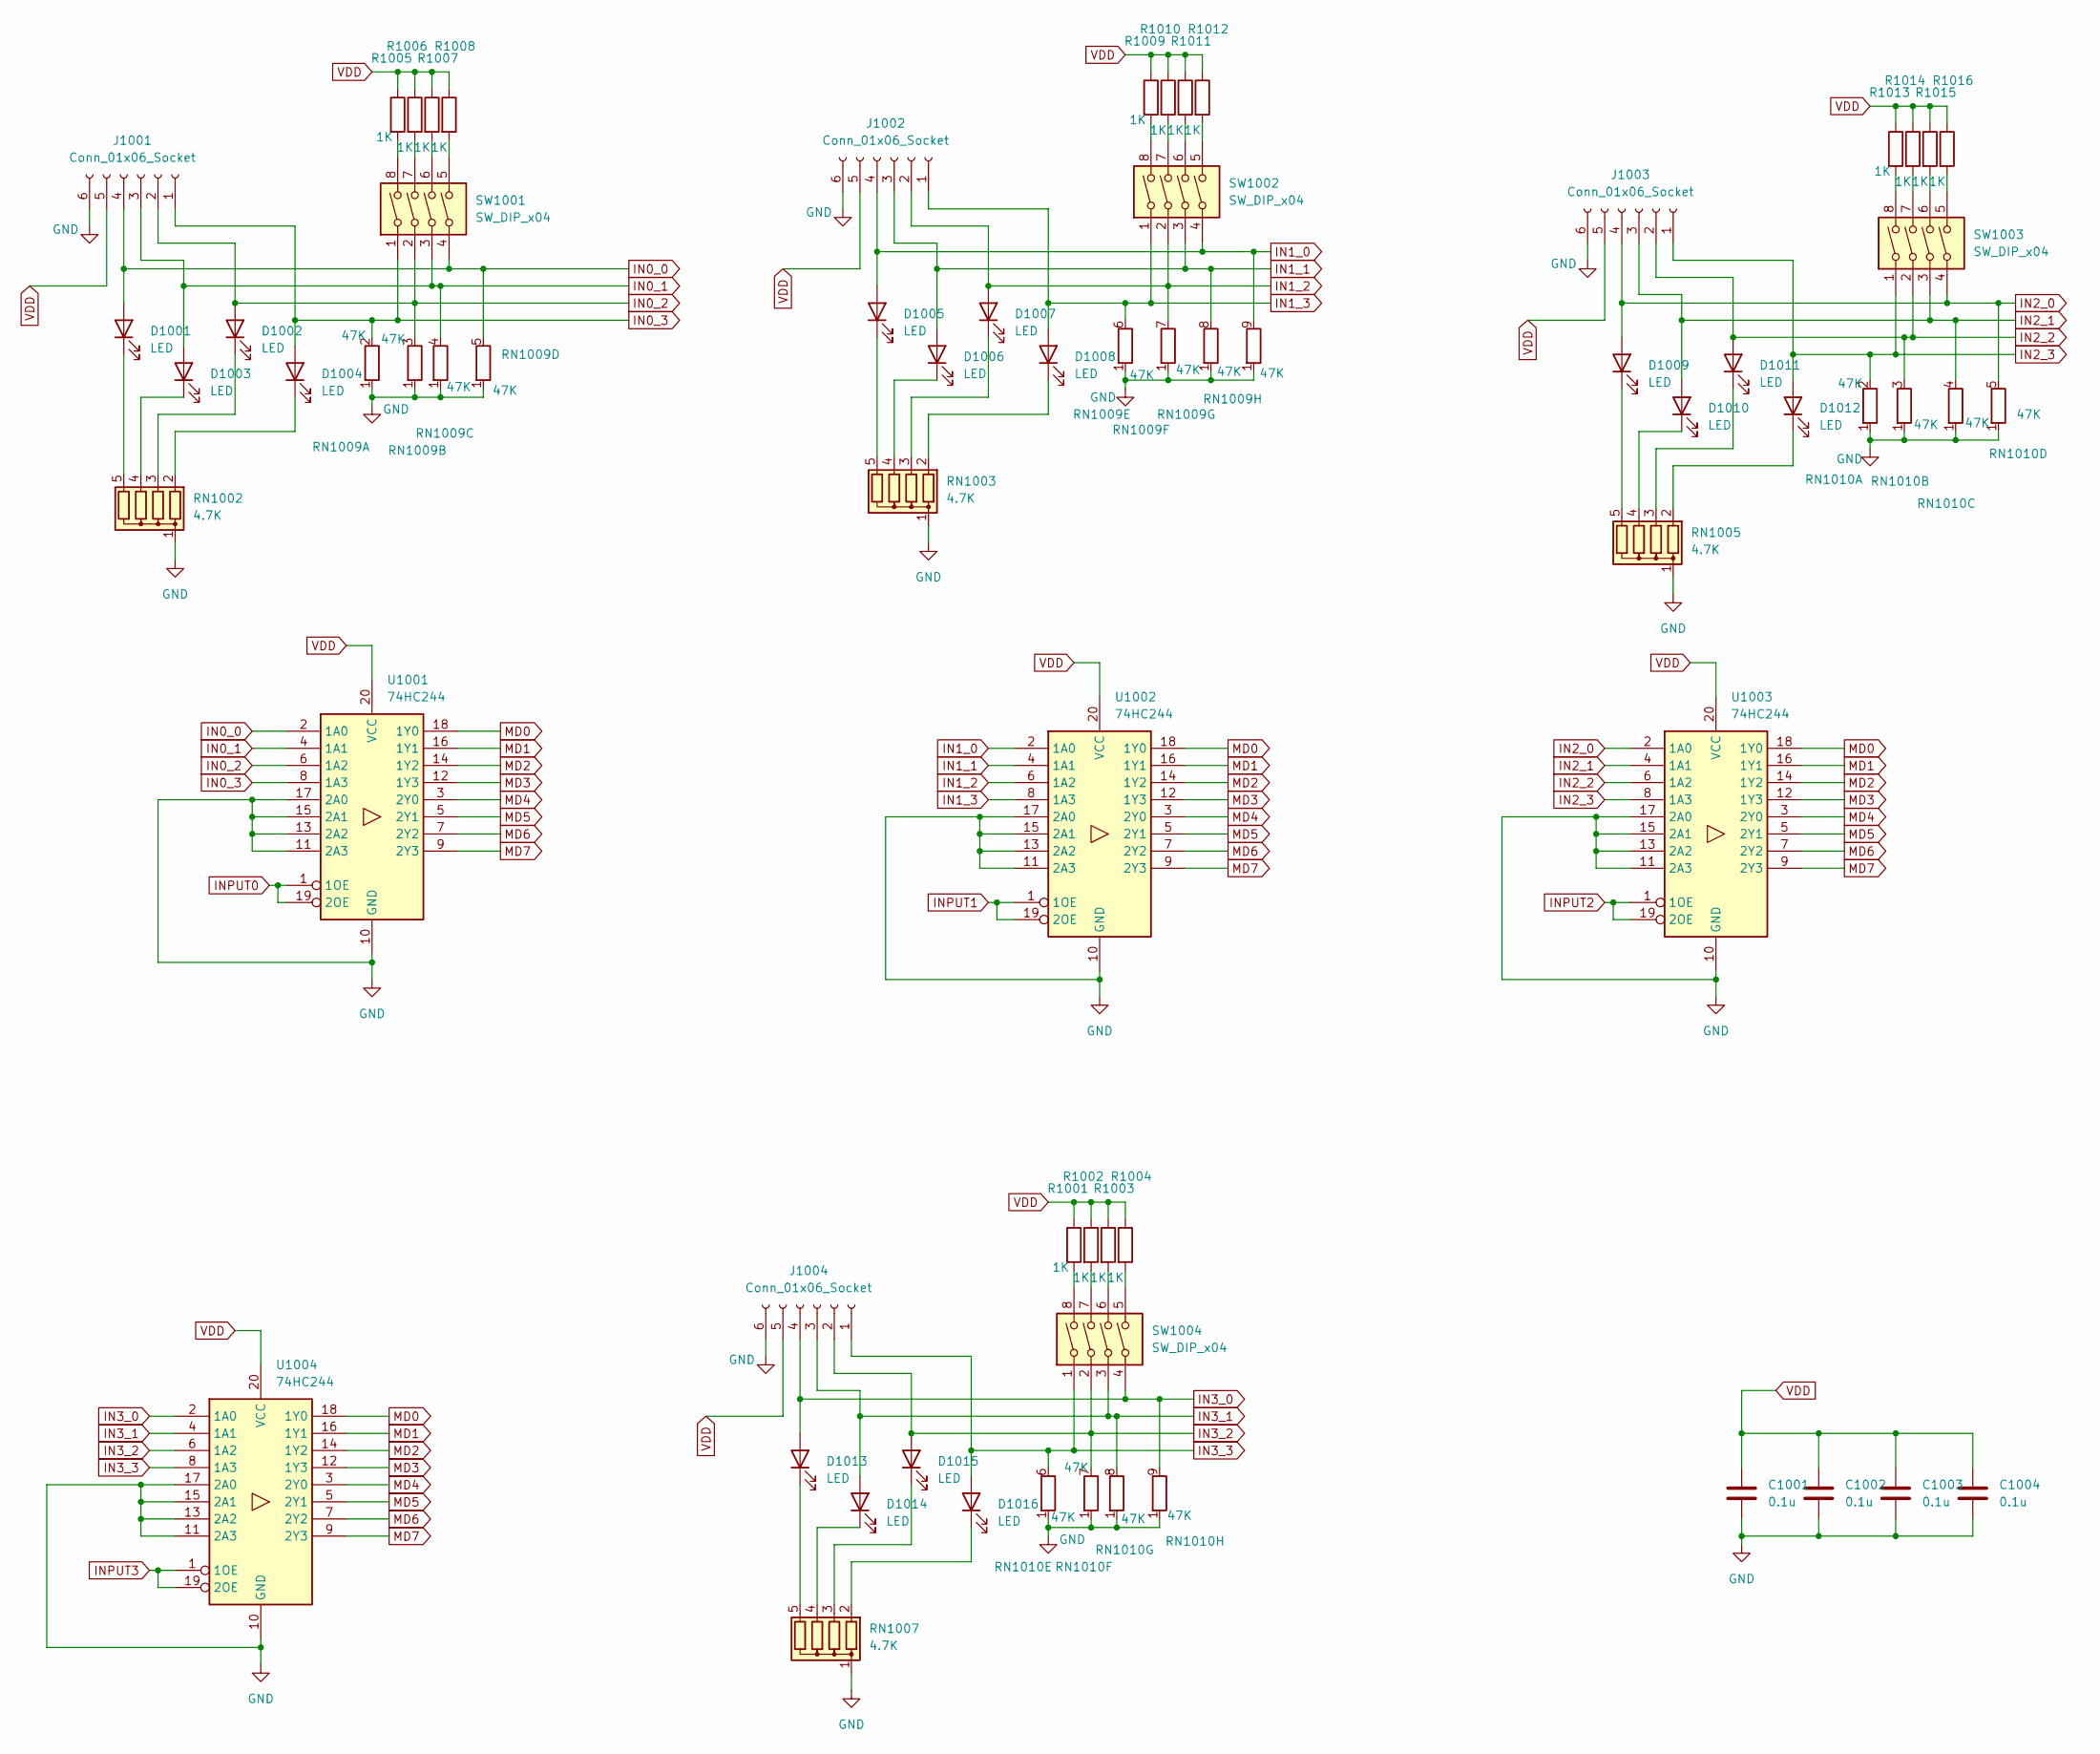
[picture p47: schematic inPut.kicad_sch]

Parts:
C1001, C1002, C1003, C1004: 0.1u
D1001, D1002, D1003, D1004, D1005, D1006, D1007, D1008, D1009, D1010, D1011, D1012, D1013, D1014, D1015, D1016: LED; LED_D3.0mm_Clear
J1001, J1002, J1003, J1004: Conn_01x06_Socket; PinSocket_1x06_P2.54mm_Vertical
R1001, R1002, R1003, R1004, R1005, R1006, R1007, R1008, R1009, R1010, R1011, R1012, R1013, R1014, R1015, R1016: 1K
RN1002, RN1003, RN1005, RN1007: 4.7K; R_Array_SIP5
RN1009, RN1010: 47K; R_Array_SIP9
SW1001, SW1002, SW1003, SW1004: SW_DIP_x04; SW_DIP_SPSTx04_Slide_9.78x12.34mm_W7.62mm_P2.54mm
U1001, U1002, U1003, U1004: 74HC244

Connections:
GND: C1001.1, C1002.1, C1003.1, C1004.1, J1001.6, J1002.6, J1003.6, J1004.6, RN1002.1 (common), RN1003.1 (common), RN1005.1 (common), RN1007.1 (common), RN1009.1 (R1), RN1010.1 (R1), U1001.10 (GND), U1001.11 (2A3), U1001.13 (2A2), U1001.15 (2A1), U1001.17 (2A0), U1002.10 (GND), U1002.11 (2A3), U1002.13 (2A2), U1002.15 (2A1), U1002.17 (2A0), U1003.10 (GND), U1003.11 (2A3), U1003.13 (2A2), U1003.15 (2A1), U1003.17 (2A0), U1004.10 (GND), U1004.11 (2A3), U1004.13 (2A2), U1004.15 (2A1), U1004.17 (2A0)
IN0_0: D1001.2 (A), J1001.4, RN1009.5 (R4.2), SW1001.4, U1001.2 (1A0)
IN0_1: D1003.2 (A), J1001.3, RN1009.4 (R3.2), SW1001.3, U1001.4 (1A1)
IN0_2: D1002.2 (A), J1001.2, RN1009.3 (R2.2), SW1001.2, U1001.6 (1A2)
IN0_3: D1004.2 (A), J1001.1, RN1009.2 (R1.2), SW1001.1, U1001.8 (1A3)
IN1_0: D1005.2 (A), J1002.4, RN1009.9 (R8.2), SW1002.4, U1002.2 (1A0)
IN1_1: D1006.2 (A), J1002.3, RN1009.8 (R7.2), SW1002.3, U1002.4 (1A1)
IN1_2: D1007.2 (A), J1002.2, RN1009.7 (R6.2), SW1002.2, U1002.6 (1A2)
IN1_3: D1008.2 (A), J1002.1, RN1009.6 (R5.2), SW1002.1, U1002.8 (1A3)
IN2_0: D1009.2 (A), J1003.4, RN1010.5 (R4.2), SW1003.4, U1003.2 (1A0)
IN2_1: D1010.2 (A), J1003.3, RN1010.4 (R3.2), SW1003.3, U1003.4 (1A1)
IN2_2: D1011.2 (A), J1003.2, RN1010.3 (R2.2), SW1003.2, U1003.6 (1A2)
IN2_3: D1012.2 (A), J1003.1, RN1010.2 (R1.2), SW1003.1, U1003.8 (1A3)
IN3_0: D1013.2 (A), J1004.4, RN1010.9 (R8.2), SW1004.4, U1004.2 (1A0)
IN3_1: D1014.2 (A), J1004.3, RN1010.8 (R7.2), SW1004.3, U1004.4 (1A1)
IN3_2: D1015.2 (A), J1004.2, RN1010.7 (R6.2), SW1004.2, U1004.6 (1A2)
IN3_3: D1016.2 (A), J1004.1, RN1010.6 (R5.2), SW1004.1, U1004.8 (1A3)
INPUT0: U1001.1 (1OE), U1001.19 (2OE)
INPUT1: U1002.1 (1OE), U1002.19 (2OE)
INPUT2: U1003.1 (1OE), U1003.19 (2OE)
INPUT3: U1004.1 (1OE), U1004.19 (2OE)
MD0: U1001.18 (1Y0), U1002.18 (1Y0), U1003.18 (1Y0), U1004.18 (1Y0)
MD1: U1001.16 (1Y1), U1002.16 (1Y1), U1003.16 (1Y1), U1004.16 (1Y1)
MD2: U1001.14 (1Y2), U1002.14 (1Y2), U1003.14 (1Y2), U1004.14 (1Y2)
MD3: U1001.12 (1Y3), U1002.12 (1Y3), U1003.12 (1Y3), U1004.12 (1Y3)
MD4: U1001.3 (2Y0), U1002.3 (2Y0), U1003.3 (2Y0), U1004.3 (2Y0)
MD5: U1001.5 (2Y1), U1002.5 (2Y1), U1003.5 (2Y1), U1004.5 (2Y1)
MD6: U1001.7 (2Y2), U1002.7 (2Y2), U1003.7 (2Y2), U1004.7 (2Y2)
MD7: U1001.9 (2Y3), U1002.9 (2Y3), U1003.9 (2Y3), U1004.9 (2Y3)
unnamed: D1001.1 (K), RN1002.5 (R4)
unnamed: D1002.1 (K), RN1002.3 (R2)
unnamed: D1003.1 (K), RN1002.4 (R3)
unnamed: D1004.1 (K), RN1002.2 (R1)
unnamed: D1005.1 (K), RN1003.5 (R4)
unnamed: D1006.1 (K), RN1003.4 (R3)
unnamed: D1007.1 (K), RN1003.3 (R2)
unnamed: D1008.1 (K), RN1003.2 (R1)
unnamed: D1009.1 (K), RN1005.5 (R4)
unnamed: D1010.1 (K), RN1005.4 (R3)
unnamed: D1011.1 (K), RN1005.3 (R2)
unnamed: D1012.1 (K), RN1005.2 (R1)
unnamed: D1013.1 (K), RN1007.5 (R4)
unnamed: D1014.1 (K), RN1007.4 (R3)
unnamed: D1015.1 (K), RN1007.3 (R2)
unnamed: D1016.1 (K), RN1007.2 (R1)
unnamed: R1001.2, SW1004.8
unnamed: R1002.2, SW1004.7
unnamed: R1003.2, SW1004.6
unnamed: R1004.2, SW1004.5
unnamed: R1005.2, SW1001.8
unnamed: R1006.2, SW1001.7
unnamed: R1007.2, SW1001.6
unnamed: R1008.2, SW1001.5
unnamed: R1009.2, SW1002.8
unnamed: R1010.2, SW1002.7
unnamed: R1011.2, SW1002.6
unnamed: R1012.2, SW1002.5
unnamed: R1013.2, SW1003.8
unnamed: R1014.2, SW1003.7
unnamed: R1015.2, SW1003.6
unnamed: R1016.2, SW1003.5
VDD: C1001.2, C1002.2, C1003.2, C1004.2, J1001.5, J1002.5, J1003.5, J1004.5, R1001.1, R1002.1, R1003.1, R1004.1, R1005.1, R1006.1, R1007.1, R1008.1, R1009.1, R1010.1, R1011.1, R1012.1, R1013.1, R1014.1, R1015.1, R1016.1, U1001.20 (VCC), U1002.20 (VCC), U1003.20 (VCC), U1004.20 (VCC)
