Myuu1967/TB-04/ver2/hardware/基板分割_0824/TB04_4_io/outPut.kicad_sch

## KiCad design ver2/hardware/基板分割_0824/TB04_4_io/outPut.kicad_sch (2026-08-24)

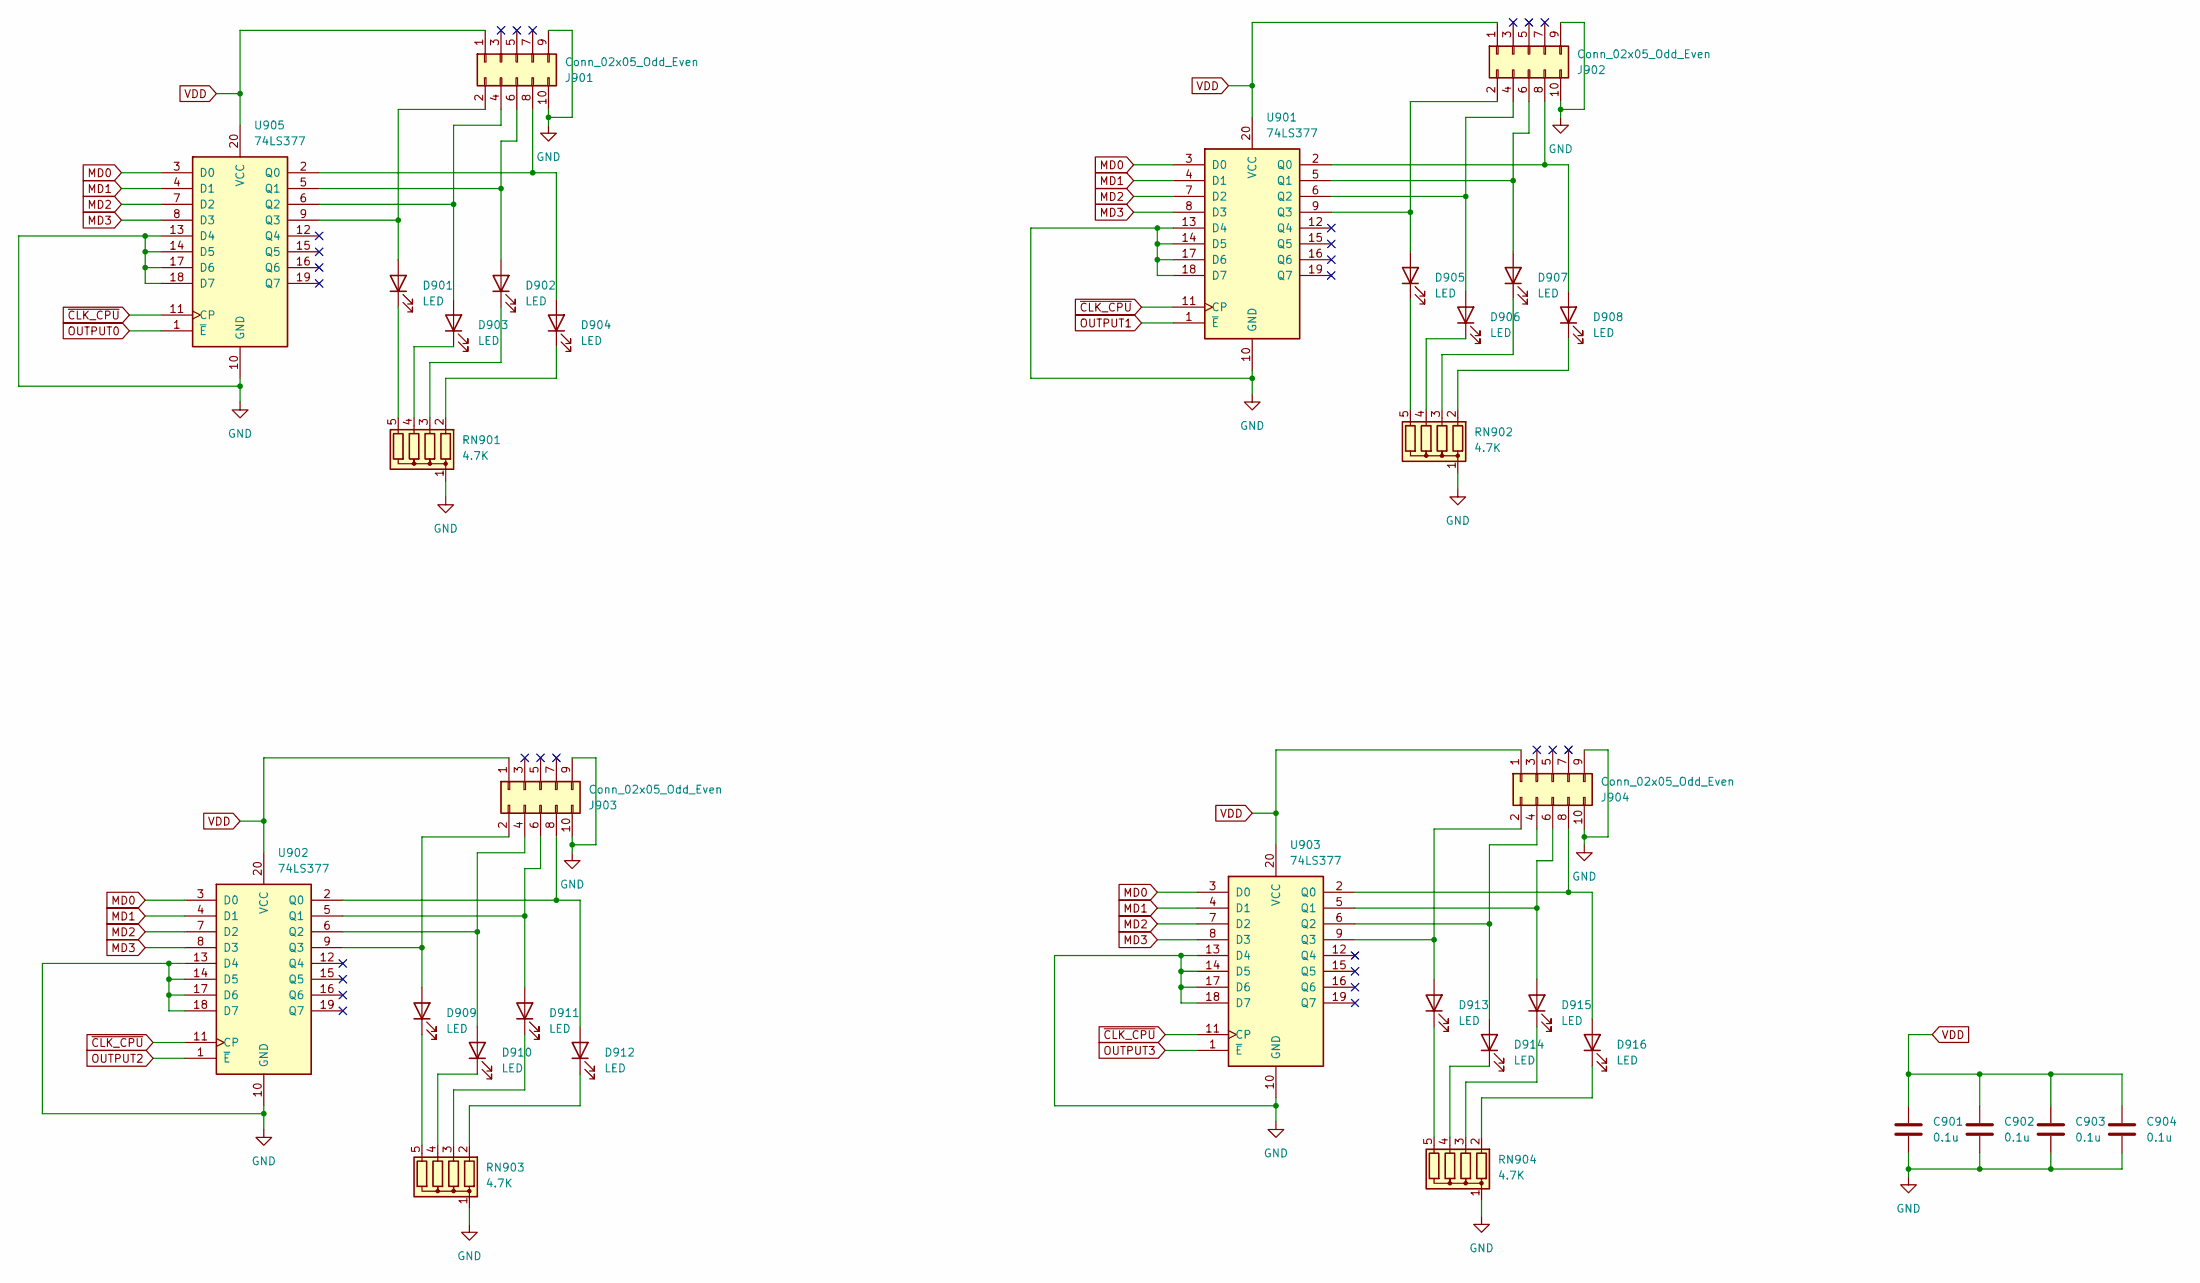
[picture p48: schematic outPut.kicad_sch]

Parts:
C901, C902, C903, C904: 0.1u
D901, D902, D903, D904, D905, D906, D907, D908, D909, D910, D911, D912, D913, D914, D915, D916: LED; LED_D3.0mm_Clear
J901, J902, J903, J904: Conn_02x05_Odd_Even
RN901, RN902, RN903, RN904: 4.7K; R_Array_SIP5
U901, U902, U903, U905: 74LS377

Connections:
GND: C901.1, C902.1, C903.1, C904.1, J901.9, J901.10, J902.9, J902.10, J903.9, J903.10, J904.9, J904.10, RN901.1 (common), RN902.1 (common), RN903.1 (common), RN904.1 (common), U901.10 (GND), U901.13 (D4), U901.14 (D5), U901.17 (D6), U901.18 (D7), U902.10 (GND), U902.13 (D4), U902.14 (D5), U902.17 (D6), U902.18 (D7), U903.10 (GND), U903.13 (D4), U903.14 (D5), U903.17 (D6), U903.18 (D7), U905.10 (GND), U905.13 (D4), U905.14 (D5), U905.17 (D6), U905.18 (D7)
MD0: U901.3 (D0), U902.3 (D0), U903.3 (D0), U905.3 (D0)
MD1: U901.4 (D1), U902.4 (D1), U903.4 (D1), U905.4 (D1)
MD2: U901.7 (D2), U902.7 (D2), U903.7 (D2), U905.7 (D2)
MD3: U901.8 (D3), U902.8 (D3), U903.8 (D3), U905.8 (D3)
unnamed: D901.1 (K), RN901.5 (R4)
unnamed: D901.2 (A), J901.2, U905.9 (Q3)
unnamed: D902.1 (K), RN901.3 (R2)
unnamed: D902.2 (A), J901.6, U905.5 (Q1)
unnamed: D903.1 (K), RN901.4 (R3)
unnamed: D903.2 (A), J901.4, U905.6 (Q2)
unnamed: D904.1 (K), RN901.2 (R1)
unnamed: D904.2 (A), J901.8, U905.2 (Q0)
unnamed: D905.1 (K), RN902.5 (R4)
unnamed: D905.2 (A), J902.2, U901.9 (Q3)
unnamed: D906.1 (K), RN902.4 (R3)
unnamed: D906.2 (A), J902.4, U901.6 (Q2)
unnamed: D907.1 (K), RN902.3 (R2)
unnamed: D907.2 (A), J902.6, U901.5 (Q1)
unnamed: D908.1 (K), RN902.2 (R1)
unnamed: D908.2 (A), J902.8, U901.2 (Q0)
unnamed: D909.1 (K), RN903.5 (R4)
unnamed: D909.2 (A), J903.2, U902.9 (Q3)
unnamed: D910.1 (K), RN903.4 (R3)
unnamed: D910.2 (A), J903.4, U902.6 (Q2)
unnamed: D911.1 (K), RN903.3 (R2)
unnamed: D911.2 (A), J903.6, U902.5 (Q1)
unnamed: D912.1 (K), RN903.2 (R1)
unnamed: D912.2 (A), J903.8, U902.2 (Q0)
unnamed: D913.1 (K), RN904.5 (R4)
unnamed: D913.2 (A), J904.2, U903.9 (Q3)
unnamed: D914.1 (K), RN904.4 (R3)
unnamed: D914.2 (A), J904.4, U903.6 (Q2)
unnamed: D915.1 (K), RN904.3 (R2)
unnamed: D915.2 (A), J904.6, U903.5 (Q1)
unnamed: D916.1 (K), RN904.2 (R1)
unnamed: D916.2 (A), J904.8, U903.2 (Q0)
OUTPUT0: U905.1 (~E)
OUTPUT1: U901.1 (~E)
OUTPUT2: U902.1 (~E)
OUTPUT3: U903.1 (~E)
VDD: C901.2, C902.2, C903.2, C904.2, J901.1, J902.1, J903.1, J904.1, U901.20 (VCC), U902.20 (VCC), U903.20 (VCC), U905.20 (VCC)
~CLK_CPU: U901.11 (CP), U902.11 (CP), U903.11 (CP), U905.11 (CP)
