Myuu1967/TB-04/ver2/hardware/基板分割_0825/TB04_IF_disp/TB04_IF_disp.kicad_sch

## KiCad design ver2/hardware/基板分割_0825/TB04_IF_disp/TB04_IF_disp.kicad_sch (2026-08-26)

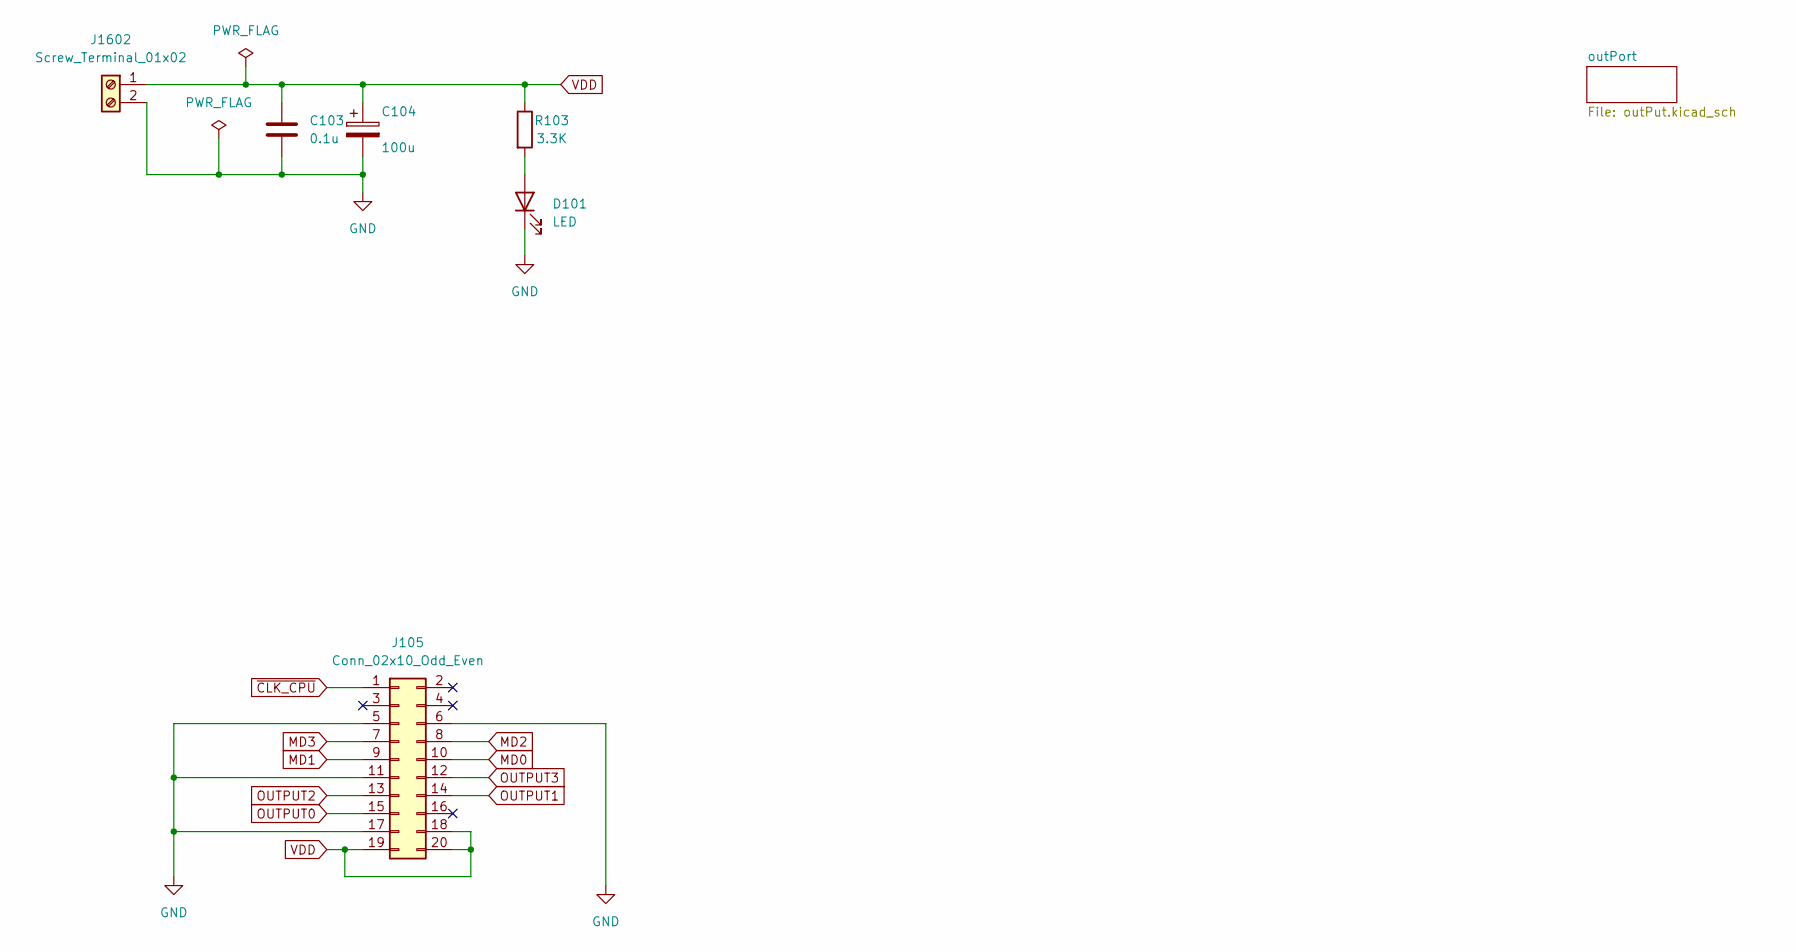
[picture p49: schematic TB04_IF_disp.kicad_sch]

Parts:
C103: 0.1u; C_Disc_D4.3mm_W1.9mm_P5.00mm
C104: 100u; CP_Radial_D5.0mm_P2.00mm
D101: LED; LED_D3.0mm_Clear
J105: Conn_02x10_Odd_Even
J1602: Screw_Terminal_01x02
R103: 3.3K; R_Axial_DIN0207_L6.3mm_D2.5mm_P7.62mm_Horizontal

Connections:
GND: C103.2, C104.2, D101.1 (K), J105.5, J105.6, J105.11, J105.17, J1602.2
MD0: J105.10
MD1: J105.9
MD2: J105.8
MD3: J105.7
unnamed: D101.2 (A), R103.2
OUTPUT0: J105.15
OUTPUT1: J105.14
OUTPUT2: J105.13
OUTPUT3: J105.12
VDD: C103.1, C104.1, J105.18, J105.19, J105.20, J1602.1, R103.1
~CLK_CPU: J105.1
