Myuu1967/TB-04/ver2/hardware/基板分割_0825/TB04_IF_in/TB04_IF_in.kicad_sch

## KiCad design ver2/hardware/基板分割_0825/TB04_IF_in/TB04_IF_in.kicad_sch (2026-08-26)

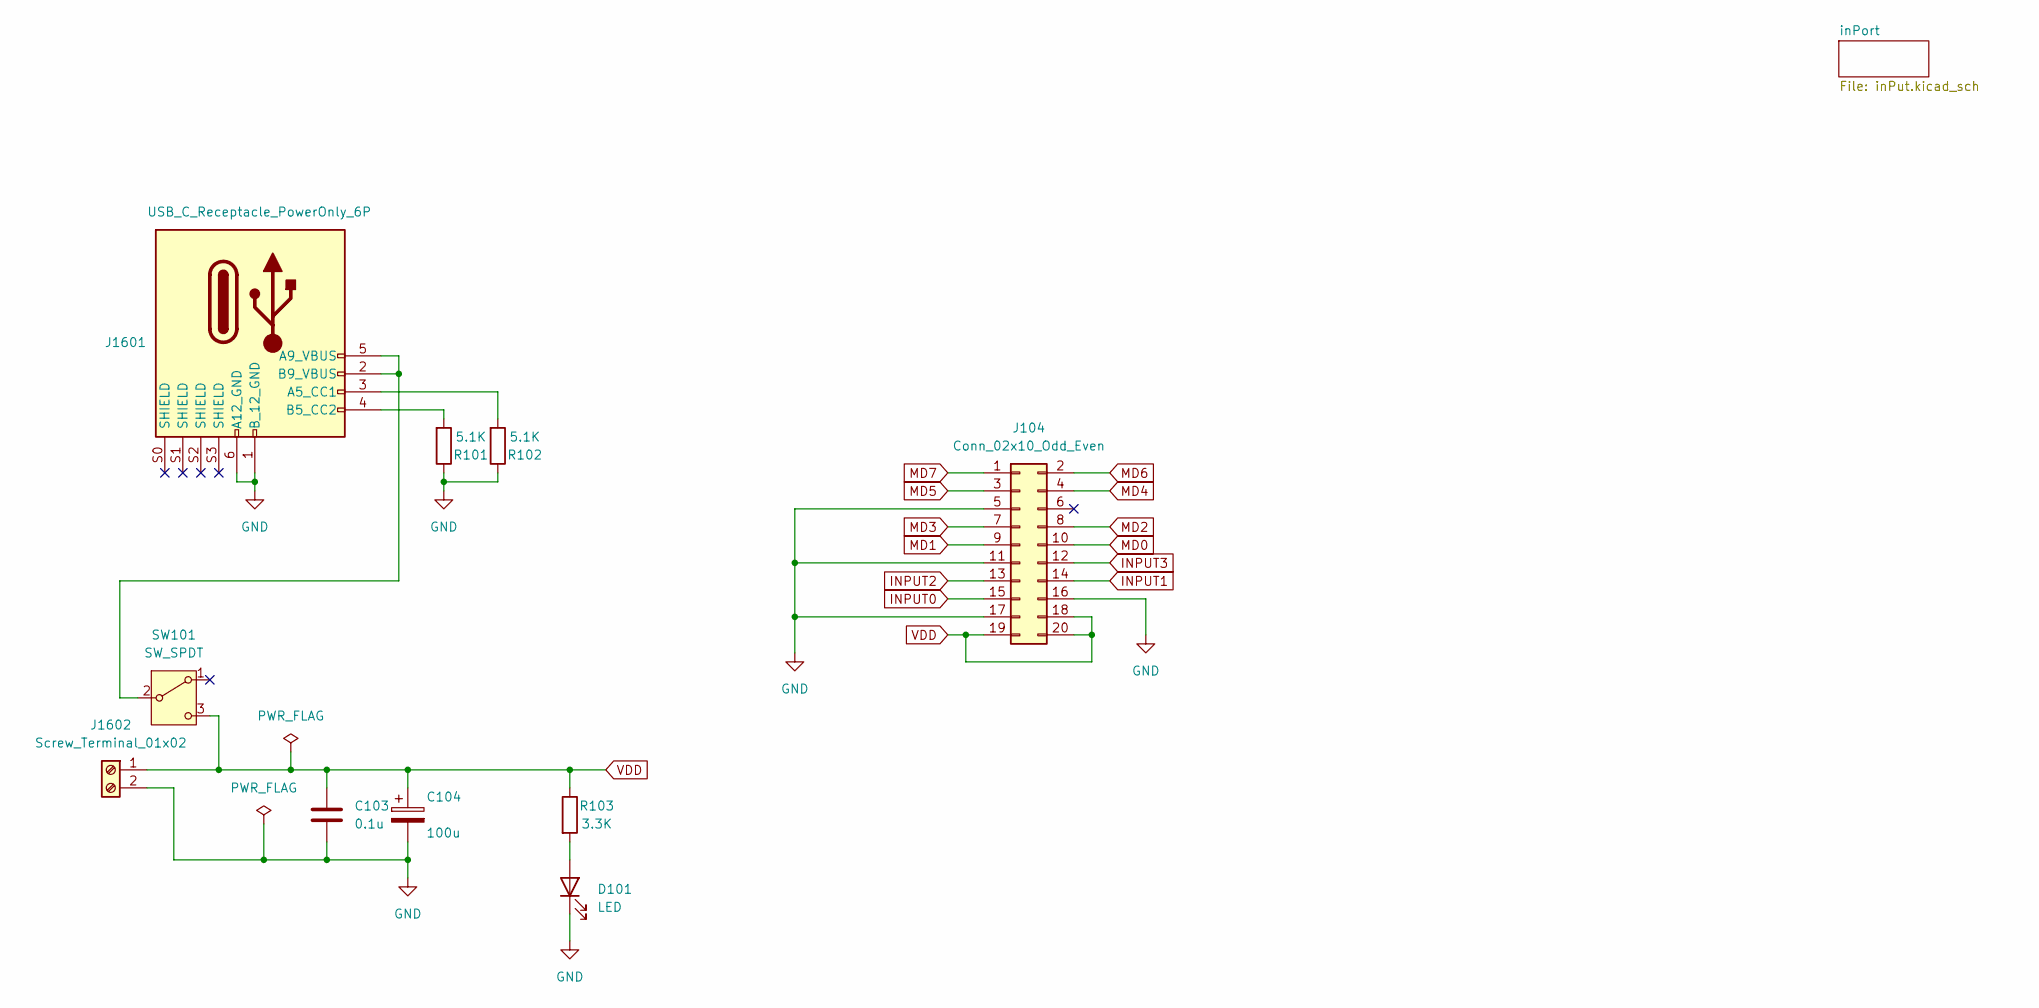
[picture p50: schematic TB04_IF_in.kicad_sch]

Parts:
C103: 0.1u; C_Disc_D4.3mm_W1.9mm_P5.00mm
C104: 100u; CP_Radial_D5.0mm_P2.00mm
D101: LED; LED_D3.0mm_Clear
J104: Conn_02x10_Odd_Even
J1601: USB_C_Receptacle_PowerOnly_6P; USB_C_receptacle_onlypower_tanuki
J1602: Screw_Terminal_01x02
R101, R102: 5.1K; R_Axial_DIN0207_L6.3mm_D2.5mm_P10.16mm_Horizontal
R103: 3.3K; R_Axial_DIN0207_L6.3mm_D2.5mm_P7.62mm_Horizontal
SW101: SW_SPDT; sw_slide

Connections:
GND: C103.2, C104.2, D101.1 (K), J104.5, J104.11, J104.16, J104.17, J1601.1 (B_12_GND), J1601.6 (A12_GND), J1602.2, R101.1, R102.1
INPUT0: J104.15
INPUT1: J104.14
INPUT2: J104.13
INPUT3: J104.12
MD0: J104.10
MD1: J104.9
MD2: J104.8
MD3: J104.7
MD4: J104.4
MD5: J104.3
MD6: J104.2
MD7: J104.1
unnamed: D101.2 (A), R103.2
unnamed: J1601.2 (B9_VBUS), J1601.5 (A9_VBUS), SW101.2 (B)
unnamed: J1601.3 (A5_CC1), R102.2
unnamed: J1601.4 (B5_CC2), R101.2
VDD: C103.1, C104.1, J104.18, J104.19, J104.20, J1602.1, R103.1, SW101.3 (C)
