Myuu1967/TB-04/ver2/hardware/基板分割_0825/TB04_S1_inst/ROM_ALU.kicad_sch

## KiCad design ver2/hardware/基板分割_0825/TB04_S1_inst/ROM_ALU.kicad_sch (2026-08-25)

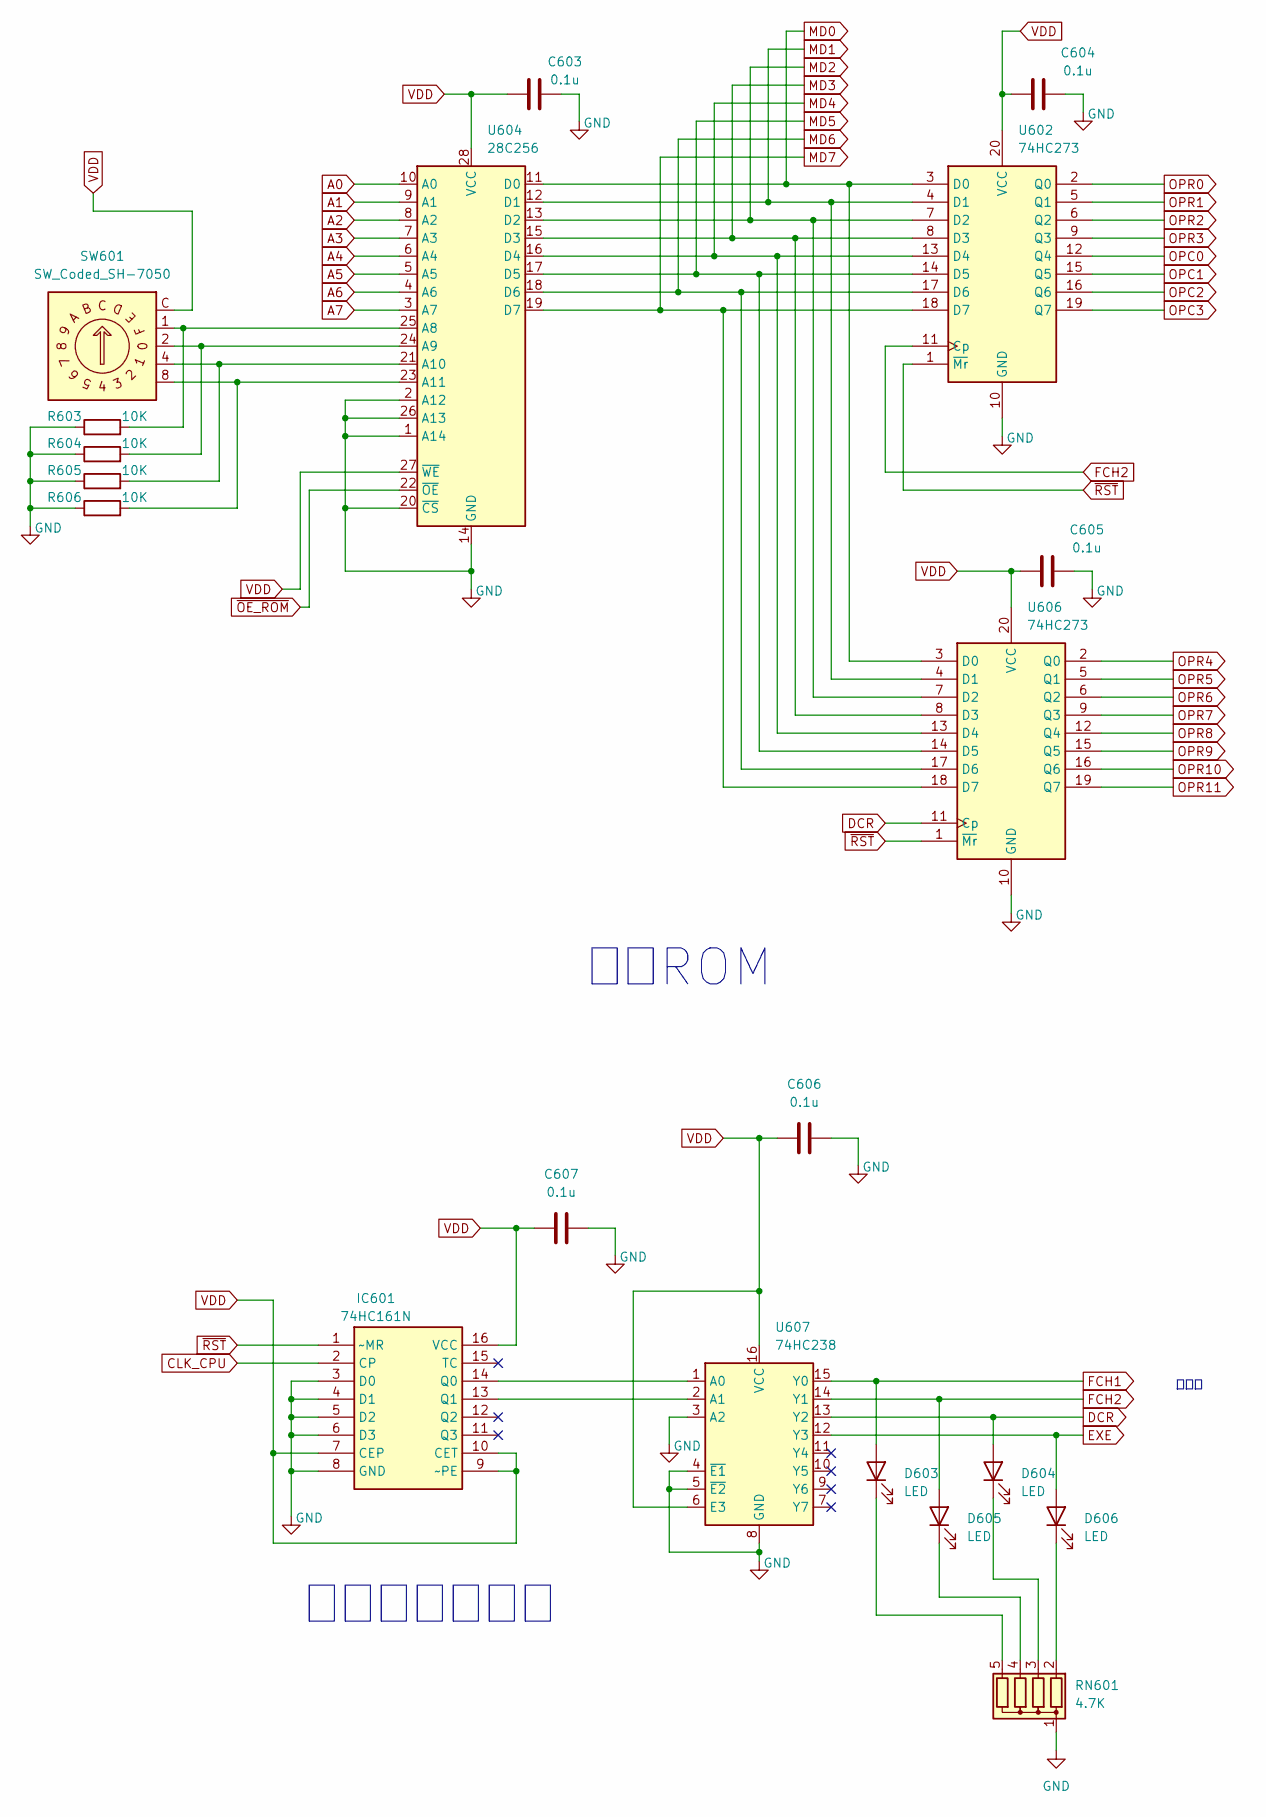
[picture p51: schematic ROM_ALU.kicad_sch]

Parts:
C603, C604, C605, C606, C607: 0.1u; C_Disc_D4.3mm_W1.9mm_P5.00mm
D603, D604, D605, D606: LED; LED_D3.0mm_Clear
IC601: 74HC161N; DIP-16_W7.62mm_Socket; Manufacturer_Part_Number 74HC161N
R603, R604, R605, R606: 10K
RN601: 4.7K; R_Array_SIP5
SW601: SW_Coded_SH-7050
U602, U606: 74HC273; DIP-20_W7.62mm_Socket
U604: 28C256; DIP_Socket-28_W11.9mm_W12.7mm_W15.24mm_W17.78mm_W18.5mm_3M_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
U607: 74HC238; DIP-16_W7.62mm_Socket

Connections:
A0: U604.10 (A0)
A1: U604.9 (A1)
A2: U604.8 (A2)
A3: U604.7 (A3)
A4: U604.6 (A4)
A5: U604.5 (A5)
A6: U604.4 (A6)
A7: U604.3 (A7)
CLK_CPU: IC601.2 (CP)
DCR: D604.2 (A), U606.11 (Cp), U607.13 (Y2)
EXE: D606.2 (A), U607.12 (Y3)
FCH1: D603.2 (A), U607.15 (Y0)
FCH2: D605.2 (A), U602.11 (Cp), U607.14 (Y1)
GND: C603.1, C604.1, C605.1, C606.2, C607.2, IC601.3 (D0), IC601.4 (D1), IC601.5 (D2), IC601.6 (D3), IC601.8 (GND), R603.1, R604.1, R605.1, R606.1, RN601.1 (common), U602.10 (GND), U604.1 (A14), U604.2 (A12), U604.14 (GND), U604.20 (~CS), U604.26 (A13), U606.10 (GND), U607.3 (A2), U607.4 (~E1), U607.5 (~E2), U607.8 (GND)
MD0: U602.3 (D0), U604.11 (D0), U606.3 (D0)
MD1: U602.4 (D1), U604.12 (D1), U606.4 (D1)
MD2: U602.7 (D2), U604.13 (D2), U606.7 (D2)
MD3: U602.8 (D3), U604.15 (D3), U606.8 (D3)
MD4: U602.13 (D4), U604.16 (D4), U606.13 (D4)
MD5: U602.14 (D5), U604.17 (D5), U606.14 (D5)
MD6: U602.17 (D6), U604.18 (D6), U606.17 (D6)
MD7: U602.18 (D7), U604.19 (D7), U606.18 (D7)
unnamed: D603.1 (K), RN601.5 (R4)
unnamed: D604.1 (K), RN601.3 (R2)
unnamed: D605.1 (K), RN601.4 (R3)
unnamed: D606.1 (K), RN601.2 (R1)
unnamed: IC601.13 (Q1), U607.2 (A1)
unnamed: IC601.14 (Q0), U607.1 (A0)
unnamed: R603.2, SW601.1, U604.25 (A8)
unnamed: R604.2, SW601.2, U604.24 (A9)
unnamed: R605.2, SW601.4, U604.21 (A10)
unnamed: R606.2, SW601.8, U604.23 (A11)
OPC0: U602.12 (Q4)
OPC1: U602.15 (Q5)
OPC2: U602.16 (Q6)
OPC3: U602.19 (Q7)
OPR0: U602.2 (Q0)
OPR1: U602.5 (Q1)
OPR2: U602.6 (Q2)
OPR3: U602.9 (Q3)
OPR4: U606.2 (Q0)
OPR5: U606.5 (Q1)
OPR6: U606.6 (Q2)
OPR7: U606.9 (Q3)
OPR8: U606.12 (Q4)
OPR9: U606.15 (Q5)
OPR10: U606.16 (Q6)
OPR11: U606.19 (Q7)
VDD: C603.2, C604.2, C605.2, C606.1, C607.1, IC601.7 (CEP), IC601.9 (~PE), IC601.10 (CET), IC601.16 (VCC), SW601.C, U602.20 (VCC), U604.27 (~WE), U604.28 (VCC), U606.20 (VCC), U607.6 (E3), U607.16 (VCC)
~OE_ROM: U604.22 (~OE)
~RST: IC601.1 (~MR), U602.1 (~Mr), U606.1 (~Mr)

Notes on the sheet:
命令ROM
フェーズ発生器
正論理
