Myuu1967/TB-04/ver2/hardware/基板分割_0825/TB04_S3_reg/PC.kicad_sch

## KiCad design ver2/hardware/基板分割_0825/TB04_S3_reg/PC.kicad_sch (2026-08-25)

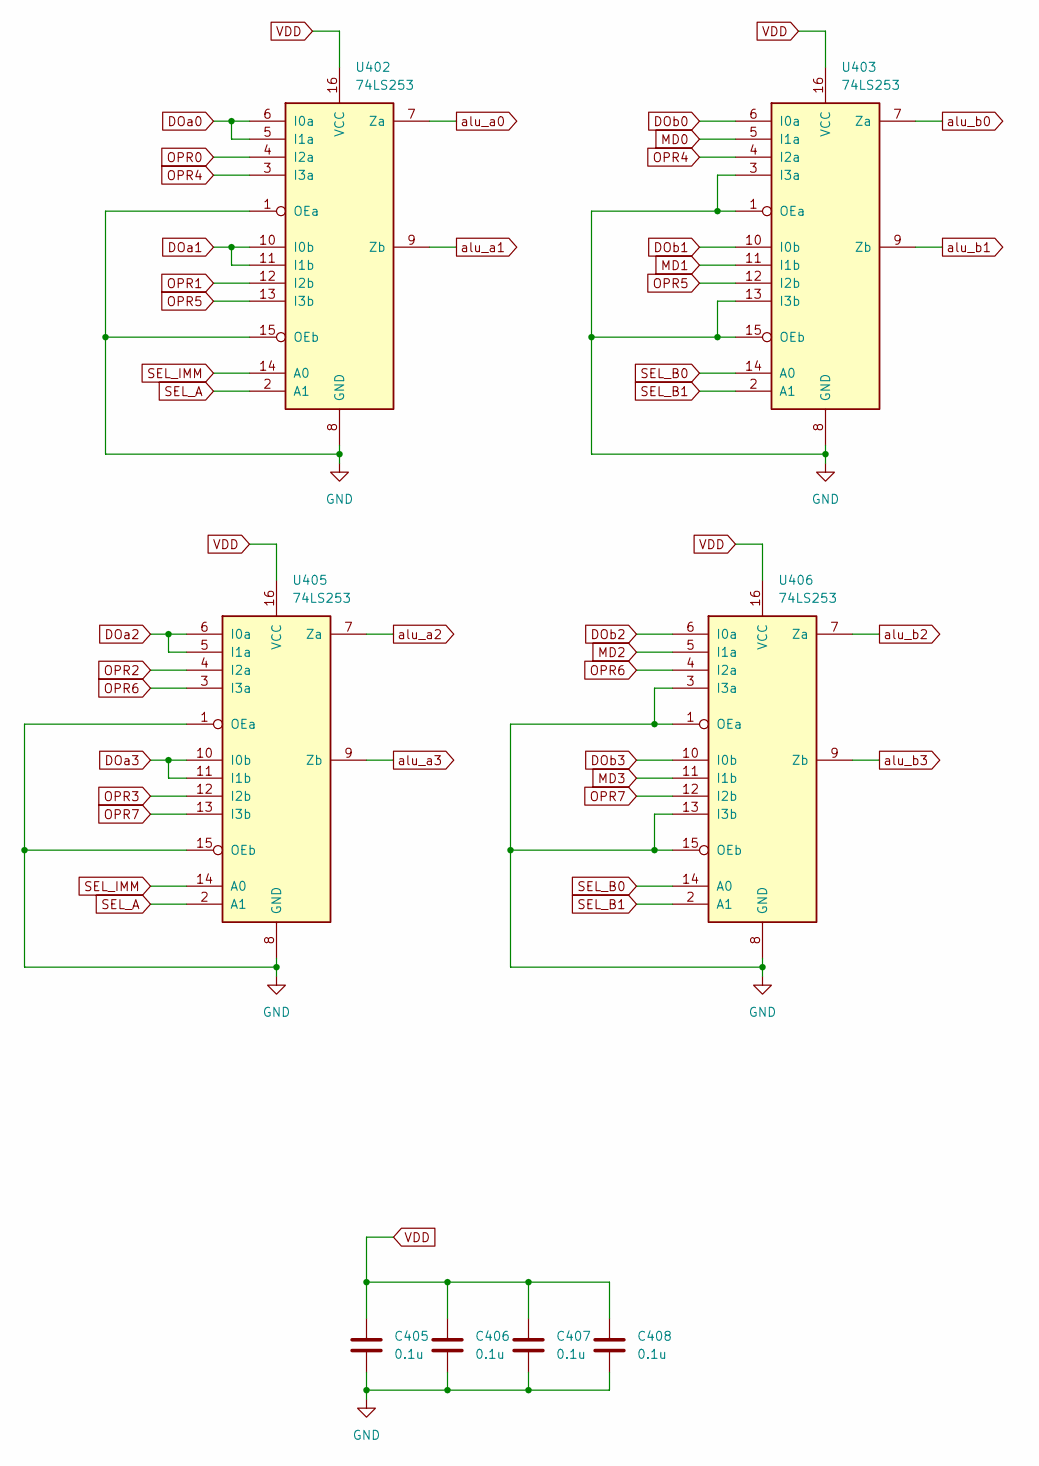
[picture p52: schematic PC.kicad_sch]

Parts:
C405, C406, C407, C408: 0.1u
U402, U403, U405, U406: 74LS253; DIP-16_W7.62mm_Socket

Connections:
DOa0: U402.5 (I1a), U402.6 (I0a)
DOa1: U402.10 (I0b), U402.11 (I1b)
DOa2: U405.5 (I1a), U405.6 (I0a)
DOa3: U405.10 (I0b), U405.11 (I1b)
DOb0: U403.6 (I0a)
DOb1: U403.10 (I0b)
DOb2: U406.6 (I0a)
DOb3: U406.10 (I0b)
GND: C405.1, C406.1, C407.1, C408.1, U402.1 (OEa), U402.8 (GND), U402.15 (OEb), U403.1 (OEa), U403.3 (I3a), U403.8 (GND), U403.13 (I3b), U403.15 (OEb), U405.1 (OEa), U405.8 (GND), U405.15 (OEb), U406.1 (OEa), U406.3 (I3a), U406.8 (GND), U406.13 (I3b), U406.15 (OEb)
MD0: U403.5 (I1a)
MD1: U403.11 (I1b)
MD2: U406.5 (I1a)
MD3: U406.11 (I1b)
OPR0: U402.4 (I2a)
OPR1: U402.12 (I2b)
OPR2: U405.4 (I2a)
OPR3: U405.12 (I2b)
OPR4: U402.3 (I3a), U403.4 (I2a)
OPR5: U402.13 (I3b), U403.12 (I2b)
OPR6: U405.3 (I3a), U406.4 (I2a)
OPR7: U405.13 (I3b), U406.12 (I2b)
SEL_A: U402.2 (A1), U405.2 (A1)
SEL_B0: U403.14 (A0), U406.14 (A0)
SEL_B1: U403.2 (A1), U406.2 (A1)
SEL_IMM: U402.14 (A0), U405.14 (A0)
VDD: C405.2, C406.2, C407.2, C408.2, U402.16 (VCC), U403.16 (VCC), U405.16 (VCC), U406.16 (VCC)
alu_a0: U402.7 (Za)
alu_a1: U402.9 (Zb)
alu_a2: U405.7 (Za)
alu_a3: U405.9 (Zb)
alu_b0: U403.7 (Za)
alu_b1: U403.9 (Zb)
alu_b2: U406.7 (Za)
alu_b3: U406.9 (Zb)
