Myuu1967/TB-04/ver2/hardware/基板分割_0825/TB04_S3_reg/RS00.kicad_sch

## KiCad design ver2/hardware/基板分割_0825/TB04_S3_reg/RS00.kicad_sch (2026-08-25)

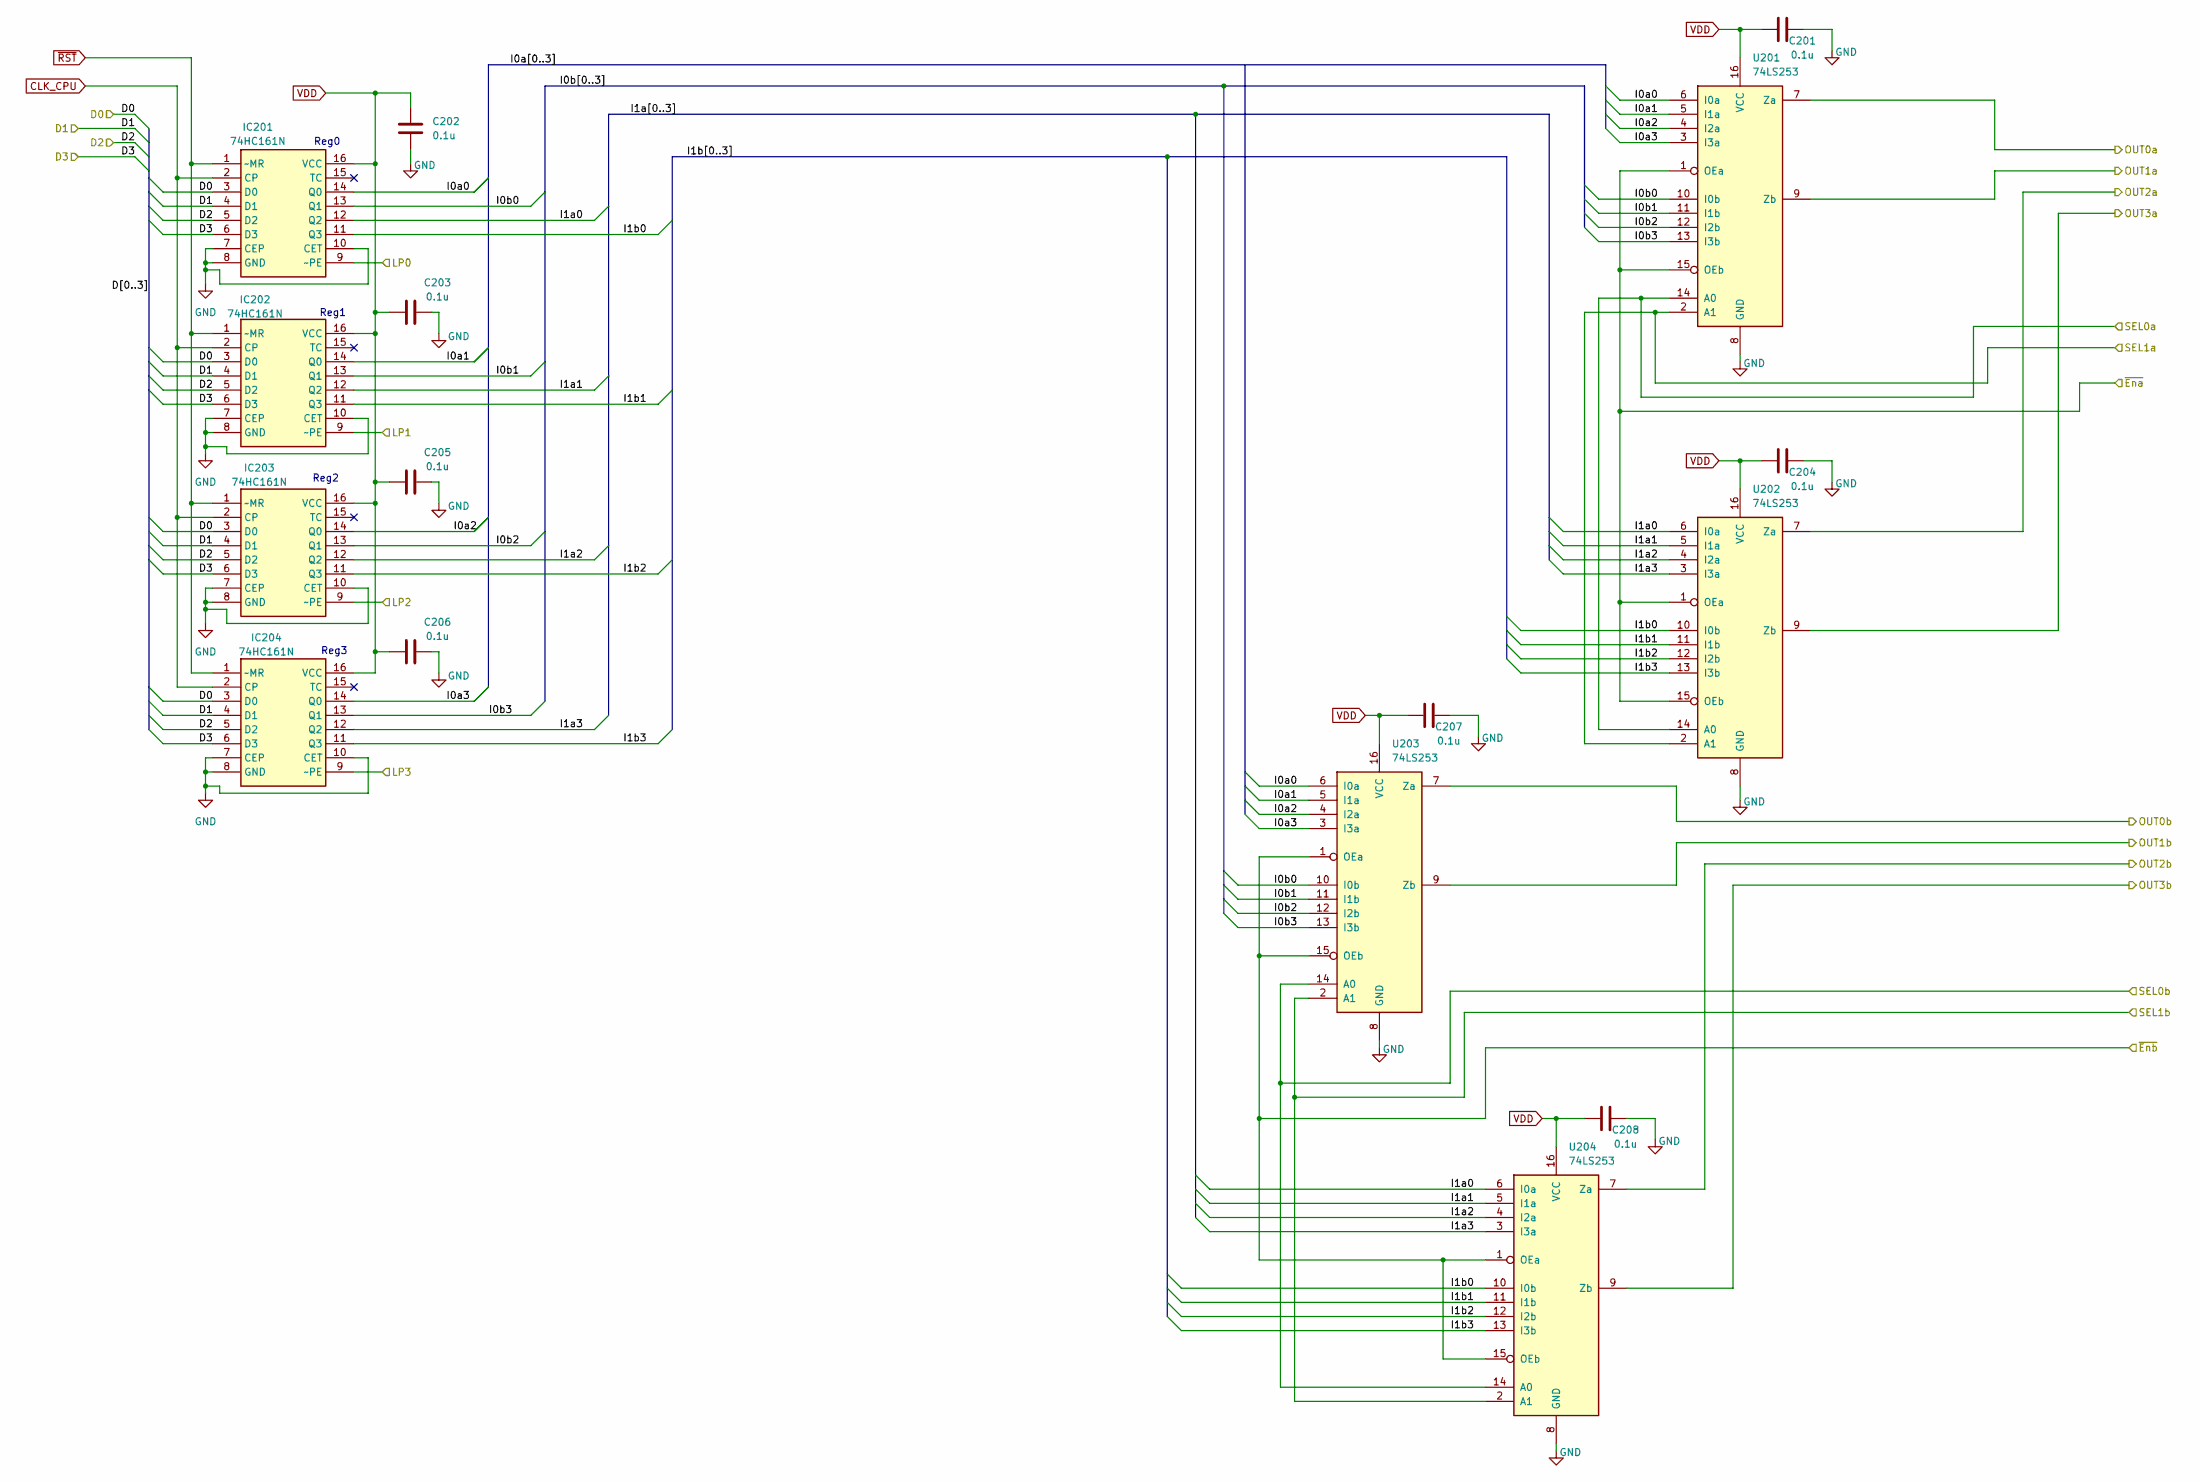
[picture p53: schematic RS00.kicad_sch]

Parts:
C201, C202, C203, C204, C205, C206, C207, C208: 0.1u; C_Disc_D4.3mm_W1.9mm_P5.00mm
IC201, IC202, IC203, IC204: 74HC161N; DIP-16_W7.62mm_Socket; Manufacturer_Part_Number 74HC161N
U201, U202, U203, U204: 74LS253; DIP-16_W7.62mm_Socket

Connections:
CLK_CPU: IC201.2 (CP), IC202.2 (CP), IC203.2 (CP), IC204.2 (CP)
D0: IC201.3 (D0), IC202.3 (D0), IC203.3 (D0), IC204.3 (D0)
D1: IC201.4 (D1), IC202.4 (D1), IC203.4 (D1), IC204.4 (D1)
D2: IC201.5 (D2), IC202.5 (D2), IC203.5 (D2), IC204.5 (D2)
D3: IC201.6 (D3), IC202.6 (D3), IC203.6 (D3), IC204.6 (D3)
GND: C201.1, C202.1, C203.1, C204.1, C205.1, C206.1, C207.1, C208.1, IC201.7 (CEP), IC201.8 (GND), IC201.10 (CET), IC202.7 (CEP), IC202.8 (GND), IC202.10 (CET), IC203.7 (CEP), IC203.8 (GND), IC203.10 (CET), IC204.7 (CEP), IC204.8 (GND), IC204.10 (CET), U201.8 (GND), U202.8 (GND), U203.8 (GND), U204.8 (GND)
I0a0: IC201.14 (Q0), U201.6 (I0a), U203.6 (I0a)
I0a1: IC202.14 (Q0), U201.5 (I1a), U203.5 (I1a)
I0a2: IC203.14 (Q0), U201.4 (I2a), U203.4 (I2a)
I0a3: IC204.14 (Q0), U201.3 (I3a), U203.3 (I3a)
I0b0: IC201.13 (Q1), U201.10 (I0b), U203.10 (I0b)
I0b1: IC202.13 (Q1), U201.11 (I1b), U203.11 (I1b)
I0b2: IC203.13 (Q1), U201.12 (I2b), U203.12 (I2b)
I0b3: IC204.13 (Q1), U201.13 (I3b), U203.13 (I3b)
I1a0: IC201.12 (Q2), U202.6 (I0a), U204.6 (I0a)
I1a1: IC202.12 (Q2), U202.5 (I1a), U204.5 (I1a)
I1a2: IC203.12 (Q2), U202.4 (I2a), U204.4 (I2a)
I1a3: IC204.12 (Q2), U202.3 (I3a), U204.3 (I3a)
I1b0: IC201.11 (Q3), U202.10 (I0b), U204.10 (I0b)
I1b1: IC202.11 (Q3), U202.11 (I1b), U204.11 (I1b)
I1b2: IC203.11 (Q3), U202.12 (I2b), U204.12 (I2b)
I1b3: IC204.11 (Q3), U202.13 (I3b), U204.13 (I3b)
LP0: IC201.9 (~PE)
LP1: IC202.9 (~PE)
LP2: IC203.9 (~PE)
LP3: IC204.9 (~PE)
OUT0a: U201.7 (Za)
OUT0b: U203.7 (Za)
OUT1a: U201.9 (Zb)
OUT1b: U203.9 (Zb)
OUT2a: U202.7 (Za)
OUT2b: U204.7 (Za)
OUT3a: U202.9 (Zb)
OUT3b: U204.9 (Zb)
SEL0a: U201.14 (A0), U202.14 (A0)
SEL0b: U203.14 (A0), U204.14 (A0)
SEL1a: U201.2 (A1), U202.2 (A1)
SEL1b: U203.2 (A1), U204.2 (A1)
VDD: C201.2, C202.2, C203.2, C204.2, C205.2, C206.2, C207.2, C208.2, IC201.16 (VCC), IC202.16 (VCC), IC203.16 (VCC), IC204.16 (VCC), U201.16 (VCC), U202.16 (VCC), U203.16 (VCC), U204.16 (VCC)
~Ena: U201.1 (OEa), U201.15 (OEb), U202.1 (OEa), U202.15 (OEb)
~Enb: U203.1 (OEa), U203.15 (OEb), U204.1 (OEa), U204.15 (OEb)
~RST: IC201.1 (~MR), IC202.1 (~MR), IC203.1 (~MR), IC204.1 (~MR)

Notes on the sheet:
Reg3
Reg2
Reg0
Reg1
