Myuu1967/TB-04/ver2/hardware/基板分割_0825/TB04_S3_reg/RS01.kicad_sch

## KiCad design ver2/hardware/基板分割_0825/TB04_S3_reg/RS01.kicad_sch (2026-08-25)

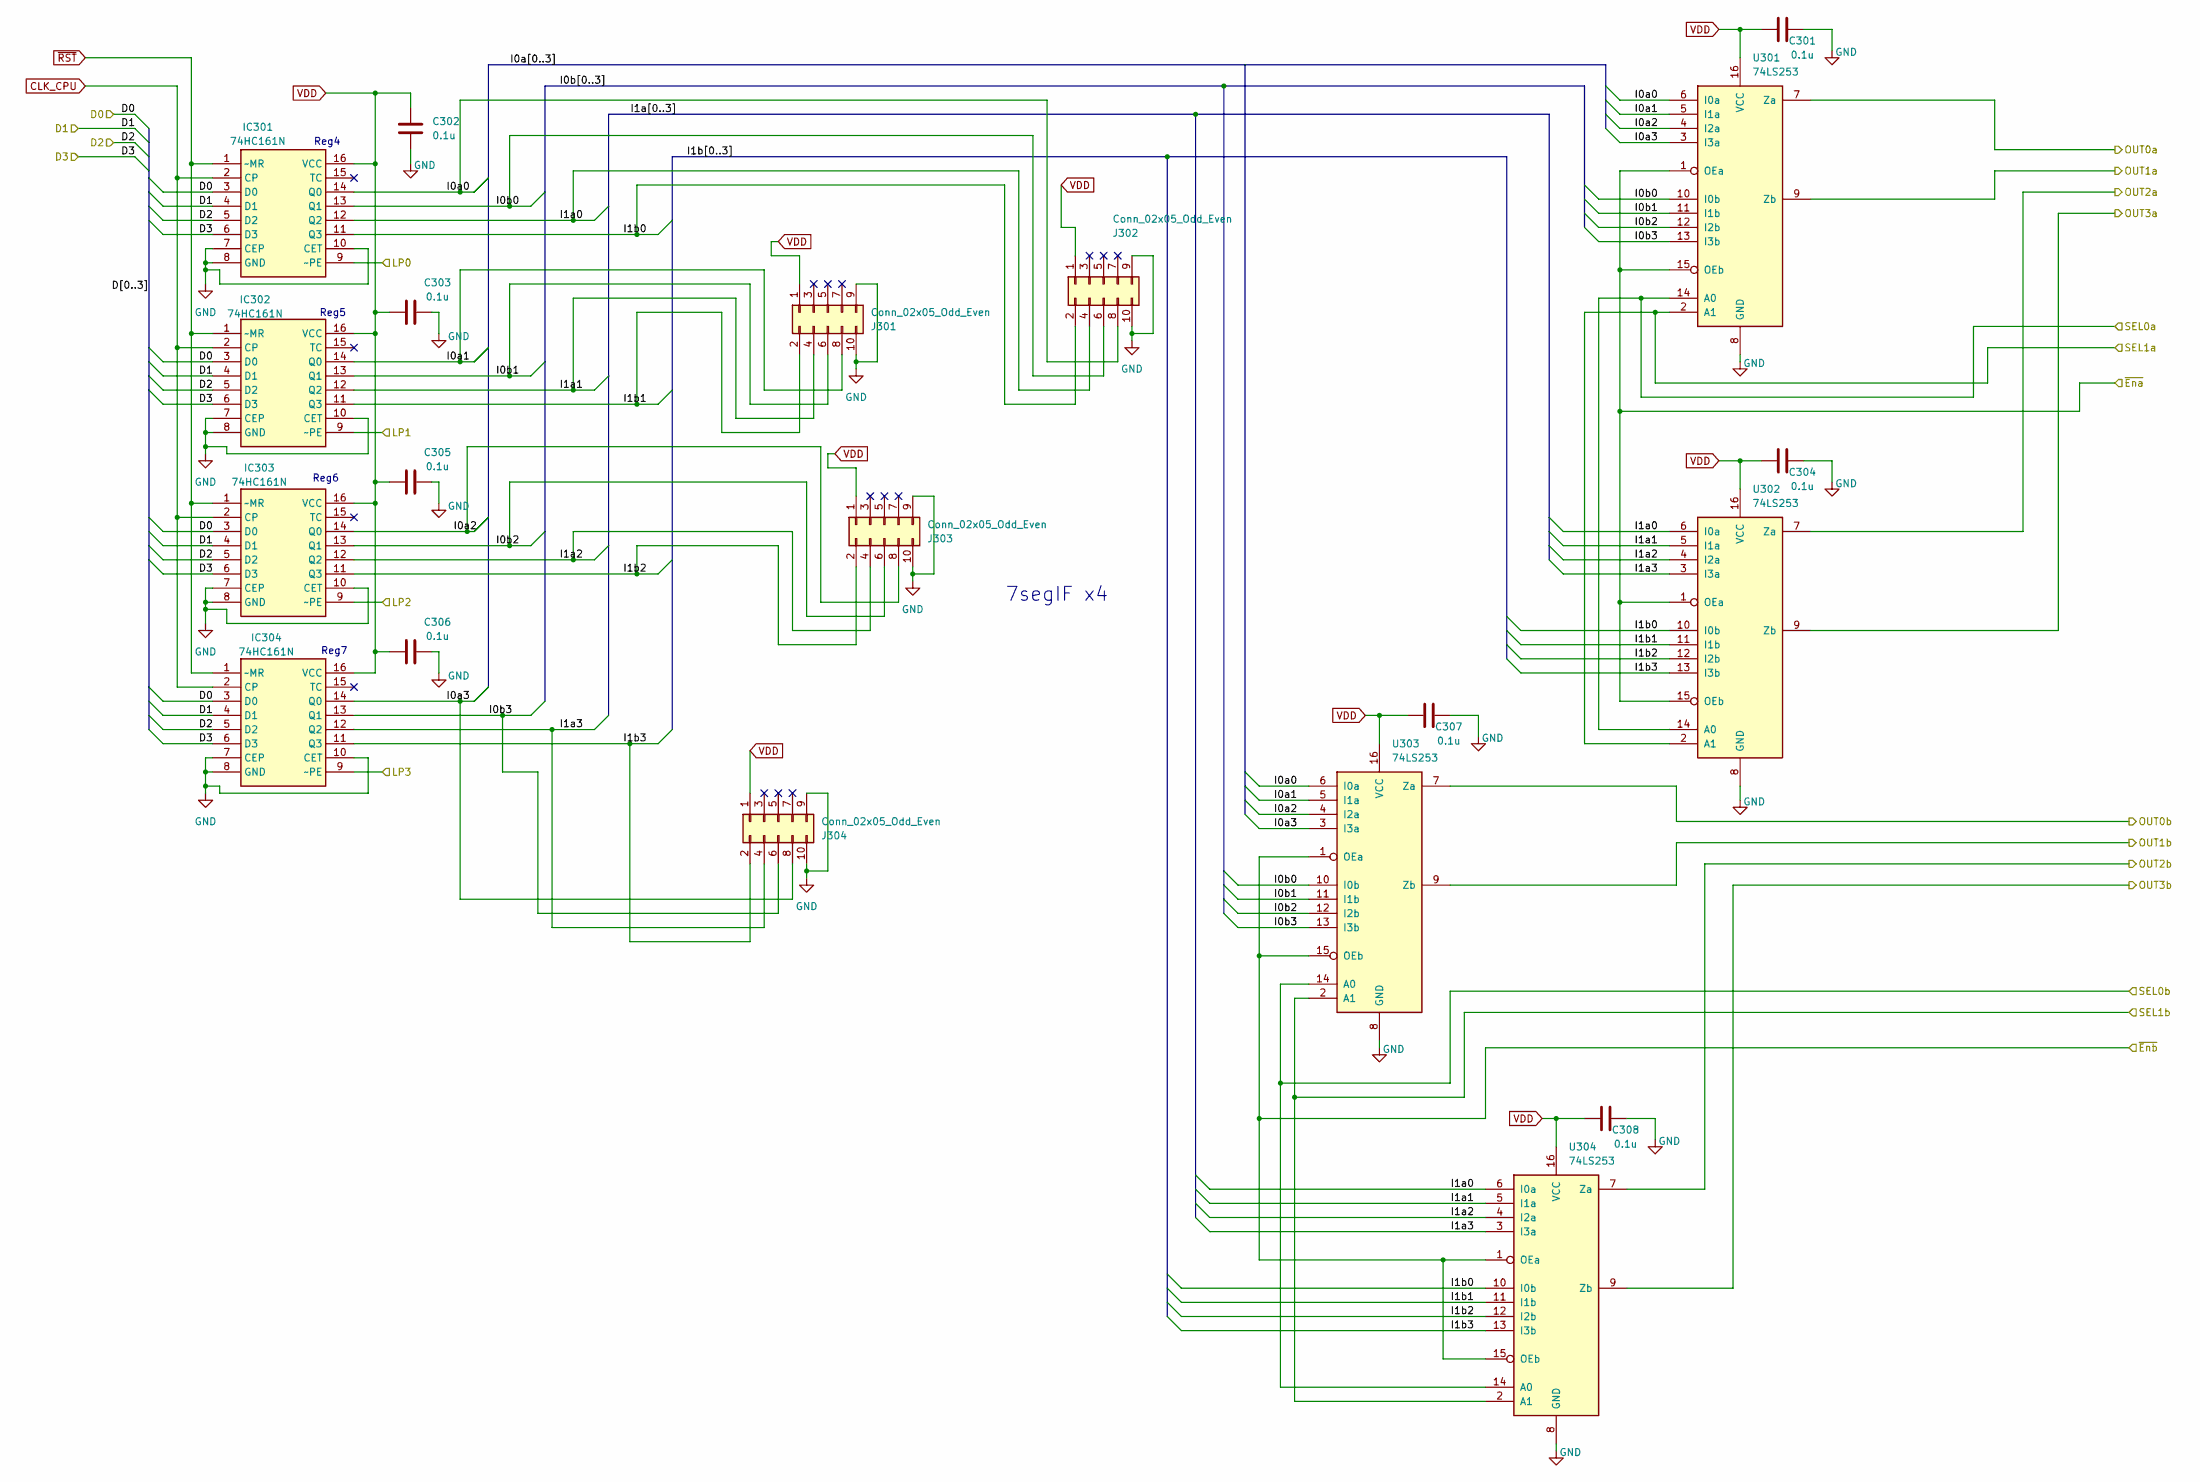
[picture p54: schematic RS01.kicad_sch]

Parts:
C301, C302, C303, C304, C305, C306, C307, C308: 0.1u; C_Disc_D4.3mm_W1.9mm_P5.00mm
IC301, IC302, IC303, IC304: 74HC161N; DIP-16_W7.62mm_Socket; Manufacturer_Part_Number 74HC161N
J301, J302, J303, J304: Conn_02x05_Odd_Even
U301, U302, U303, U304: 74LS253; DIP-16_W7.62mm_Socket

Connections:
CLK_CPU: IC301.2 (CP), IC302.2 (CP), IC303.2 (CP), IC304.2 (CP)
D0: IC301.3 (D0), IC302.3 (D0), IC303.3 (D0), IC304.3 (D0)
D1: IC301.4 (D1), IC302.4 (D1), IC303.4 (D1), IC304.4 (D1)
D2: IC301.5 (D2), IC302.5 (D2), IC303.5 (D2), IC304.5 (D2)
D3: IC301.6 (D3), IC302.6 (D3), IC303.6 (D3), IC304.6 (D3)
GND: C301.1, C302.1, C303.1, C304.1, C305.1, C306.1, C307.1, C308.1, IC301.7 (CEP), IC301.8 (GND), IC301.10 (CET), IC302.7 (CEP), IC302.8 (GND), IC302.10 (CET), IC303.7 (CEP), IC303.8 (GND), IC303.10 (CET), IC304.7 (CEP), IC304.8 (GND), IC304.10 (CET), J301.9, J301.10, J302.9, J302.10, J303.9, J303.10, J304.9, J304.10, U301.8 (GND), U302.8 (GND), U303.8 (GND), U304.8 (GND)
I0a0: IC301.14 (Q0), J302.8, U301.6 (I0a), U303.6 (I0a)
I0a1: IC302.14 (Q0), J301.8, U301.5 (I1a), U303.5 (I1a)
I0a2: IC303.14 (Q0), J303.8, U301.4 (I2a), U303.4 (I2a)
I0a3: IC304.14 (Q0), J304.8, U301.3 (I3a), U303.3 (I3a)
I0b0: IC301.13 (Q1), J302.6, U301.10 (I0b), U303.10 (I0b)
I0b1: IC302.13 (Q1), J301.6, U301.11 (I1b), U303.11 (I1b)
I0b2: IC303.13 (Q1), J303.6, U301.12 (I2b), U303.12 (I2b)
I0b3: IC304.13 (Q1), J304.6, U301.13 (I3b), U303.13 (I3b)
I1a0: IC301.12 (Q2), J302.4, U302.6 (I0a), U304.6 (I0a)
I1a1: IC302.12 (Q2), J301.4, U302.5 (I1a), U304.5 (I1a)
I1a2: IC303.12 (Q2), J303.4, U302.4 (I2a), U304.4 (I2a)
I1a3: IC304.12 (Q2), J304.4, U302.3 (I3a), U304.3 (I3a)
I1b0: IC301.11 (Q3), J302.2, U302.10 (I0b), U304.10 (I0b)
I1b1: IC302.11 (Q3), J301.2, U302.11 (I1b), U304.11 (I1b)
I1b2: IC303.11 (Q3), J303.2, U302.12 (I2b), U304.12 (I2b)
I1b3: IC304.11 (Q3), J304.2, U302.13 (I3b), U304.13 (I3b)
LP0: IC301.9 (~PE)
LP1: IC302.9 (~PE)
LP2: IC303.9 (~PE)
LP3: IC304.9 (~PE)
OUT0a: U301.7 (Za)
OUT0b: U303.7 (Za)
OUT1a: U301.9 (Zb)
OUT1b: U303.9 (Zb)
OUT2a: U302.7 (Za)
OUT2b: U304.7 (Za)
OUT3a: U302.9 (Zb)
OUT3b: U304.9 (Zb)
SEL0a: U301.14 (A0), U302.14 (A0)
SEL0b: U303.14 (A0), U304.14 (A0)
SEL1a: U301.2 (A1), U302.2 (A1)
SEL1b: U303.2 (A1), U304.2 (A1)
VDD: C301.2, C302.2, C303.2, C304.2, C305.2, C306.2, C307.2, C308.2, IC301.16 (VCC), IC302.16 (VCC), IC303.16 (VCC), IC304.16 (VCC), J301.1, J302.1, J303.1, J304.1, U301.16 (VCC), U302.16 (VCC), U303.16 (VCC), U304.16 (VCC)
~Ena: U301.1 (OEa), U301.15 (OEb), U302.1 (OEa), U302.15 (OEb)
~Enb: U303.1 (OEa), U303.15 (OEb), U304.1 (OEa), U304.15 (OEb)
~RST: IC301.1 (~MR), IC302.1 (~MR), IC303.1 (~MR), IC304.1 (~MR)

Notes on the sheet:
Reg5
Reg4
Reg7
7segIF x4
Reg6
