Myuu1967/TB-04/ver2/hardware/基板分割_0825/TB04_S4_addr/TB04_S4_addr.kicad_sch

## KiCad design ver2/hardware/基板分割_0825/TB04_S4_addr/TB04_S4_addr.kicad_sch (2026-08-26)

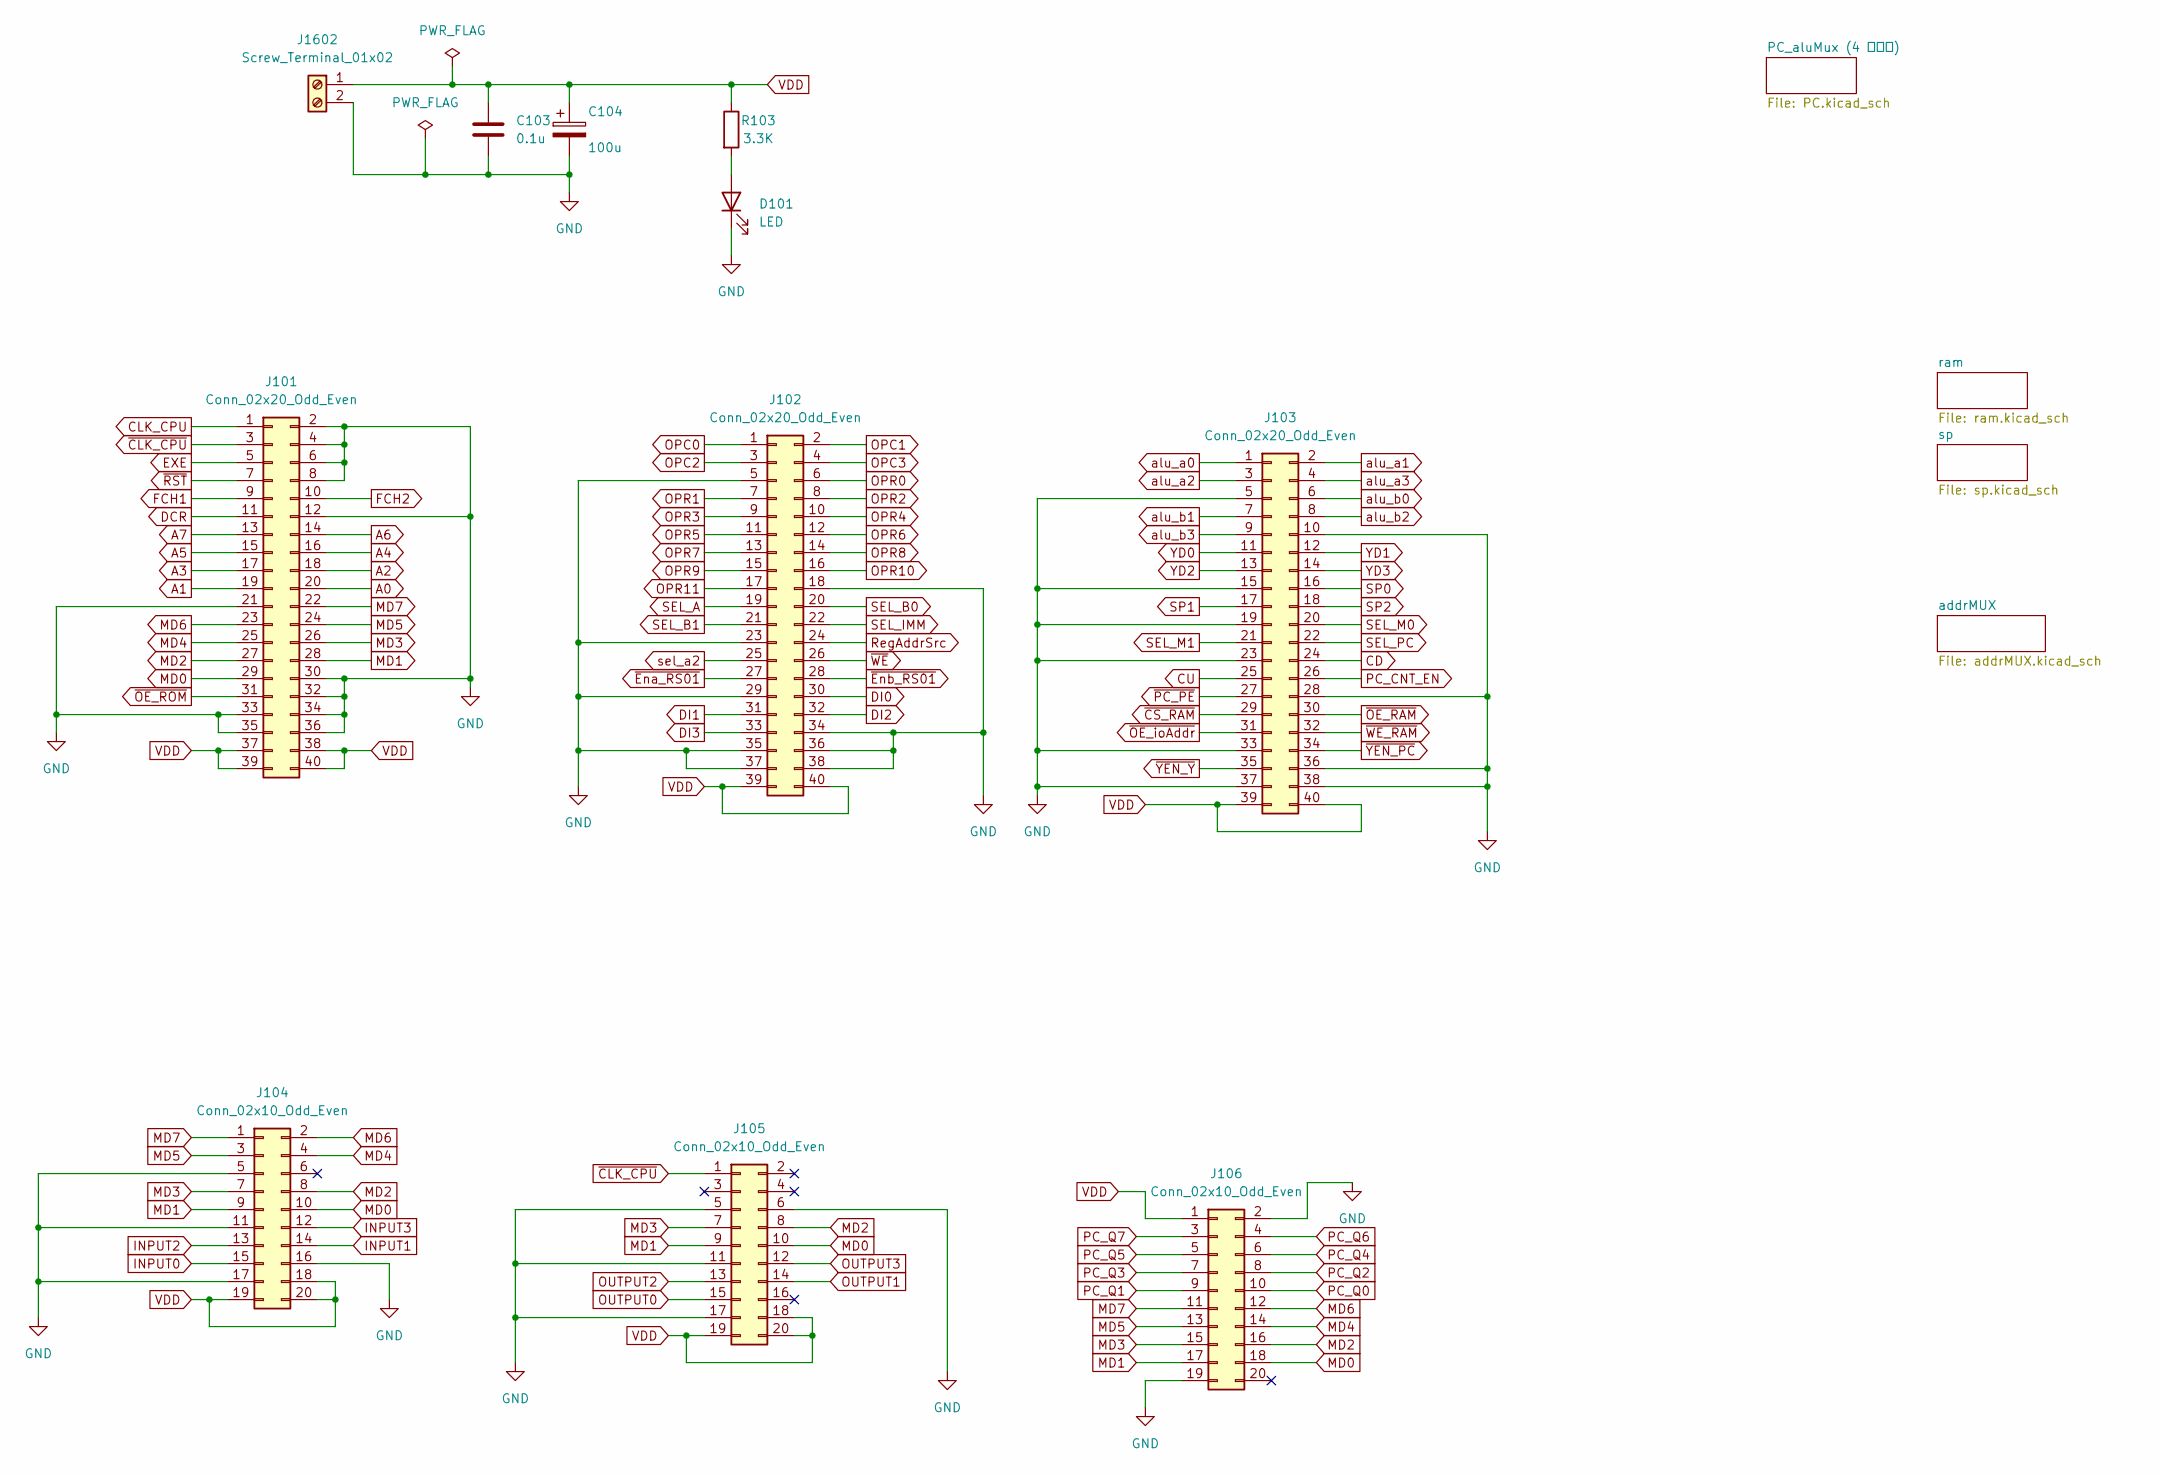
[picture p56: schematic TB04_S4_addr.kicad_sch]

Parts:
C103: 0.1u; C_Disc_D4.3mm_W1.9mm_P5.00mm
C104: 100u; CP_Radial_D5.0mm_P2.00mm
D101: LED; LED_D3.0mm_Clear
J101, J102, J103: Conn_02x20_Odd_Even
J104, J105, J106: Conn_02x10_Odd_Even
J1602: Screw_Terminal_01x02
R103: 3.3K; R_Axial_DIN0207_L6.3mm_D2.5mm_P7.62mm_Horizontal

Connections:
A0: J101.20
A1: J101.19
A2: J101.18
A3: J101.17
A4: J101.16
A5: J101.15
A6: J101.14
A7: J101.13
CD: J103.24
CLK_CPU: J101.1
CU: J103.25
DCR: J101.11
DI0: J102.30
DI1: J102.31
DI2: J102.32
DI3: J102.33
EXE: J101.5
FCH1: J101.9
FCH2: J101.10
GND: C103.2, C104.2, D101.1 (K), J101.2, J101.4, J101.6, J101.8, J101.12, J101.21, J101.30, J101.32, J101.33, J101.34, J101.35, J101.36, J102.5, J102.18, J102.23, J102.29, J102.34, J102.35, J102.36, J102.37, J102.38, J103.5, J103.10, J103.15, J103.19, J103.23, J103.28, J103.33, J103.36, J103.37, J103.38, J104.5, J104.11, J104.16, J104.17, J105.5, J105.6, J105.11, J105.17, J106.2, J106.19, J1602.2
INPUT0: J104.15
INPUT1: J104.14
INPUT2: J104.13
INPUT3: J104.12
MD0: J101.29, J104.10, J105.10, J106.18
MD1: J101.28, J104.9, J105.9, J106.17
MD2: J101.27, J104.8, J105.8, J106.16
MD3: J101.26, J104.7, J105.7, J106.15
MD4: J101.25, J104.4, J106.14
MD5: J101.24, J104.3, J106.13
MD6: J101.23, J104.2, J106.12
MD7: J101.22, J104.1, J106.11
unnamed: D101.2 (A), R103.2
OPC0: J102.1
OPC1: J102.2
OPC2: J102.3
OPC3: J102.4
OPR0: J102.6
OPR1: J102.7
OPR2: J102.8
OPR3: J102.9
OPR4: J102.10
OPR5: J102.11
OPR6: J102.12
OPR7: J102.13
OPR8: J102.14
OPR9: J102.15
OPR10: J102.16
OPR11: J102.17
OUTPUT0: J105.15
OUTPUT1: J105.14
OUTPUT2: J105.13
OUTPUT3: J105.12
PC_CNT_EN: J103.26
PC_Q0: J106.10
PC_Q1: J106.9
PC_Q2: J106.8
PC_Q3: J106.7
PC_Q4: J106.6
PC_Q5: J106.5
PC_Q6: J106.4
PC_Q7: J106.3
RegAddrSrc: J102.24
SEL_A: J102.19
SEL_B0: J102.20
SEL_B1: J102.21
SEL_IMM: J102.22
SEL_M0: J103.20
SEL_M1: J103.21
SEL_PC: J103.22
SP0: J103.16
SP1: J103.17
SP2: J103.18
VDD: C103.1, C104.1, J101.37, J101.38, J101.39, J101.40, J102.39, J102.40, J103.39, J103.40, J104.18, J104.19, J104.20, J105.18, J105.19, J105.20, J106.1, J1602.1, R103.1
YD0: J103.11
YD1: J103.12
YD2: J103.13
YD3: J103.14
alu_a0: J103.1
alu_a1: J103.2
alu_a2: J103.3
alu_a3: J103.4
alu_b0: J103.6
alu_b1: J103.7
alu_b2: J103.8
alu_b3: J103.9
sel_a2: J102.25
~CLK_CPU: J101.3, J105.1
~CS_RAM: J103.29
~Ena_RS01: J102.27
~Enb_RS01: J102.28
~OE_RAM: J103.30
~OE_ROM: J101.31
~OE_ioAddr: J103.31
~PC_PE: J103.27
~RST: J101.7
~WE_RAM: J103.32
~WE: J102.26
~YEN_PC: J103.34
~YEN_Y: J103.35
